PepperCat-YamanekoVillage/NORZ/alu/.alu.png

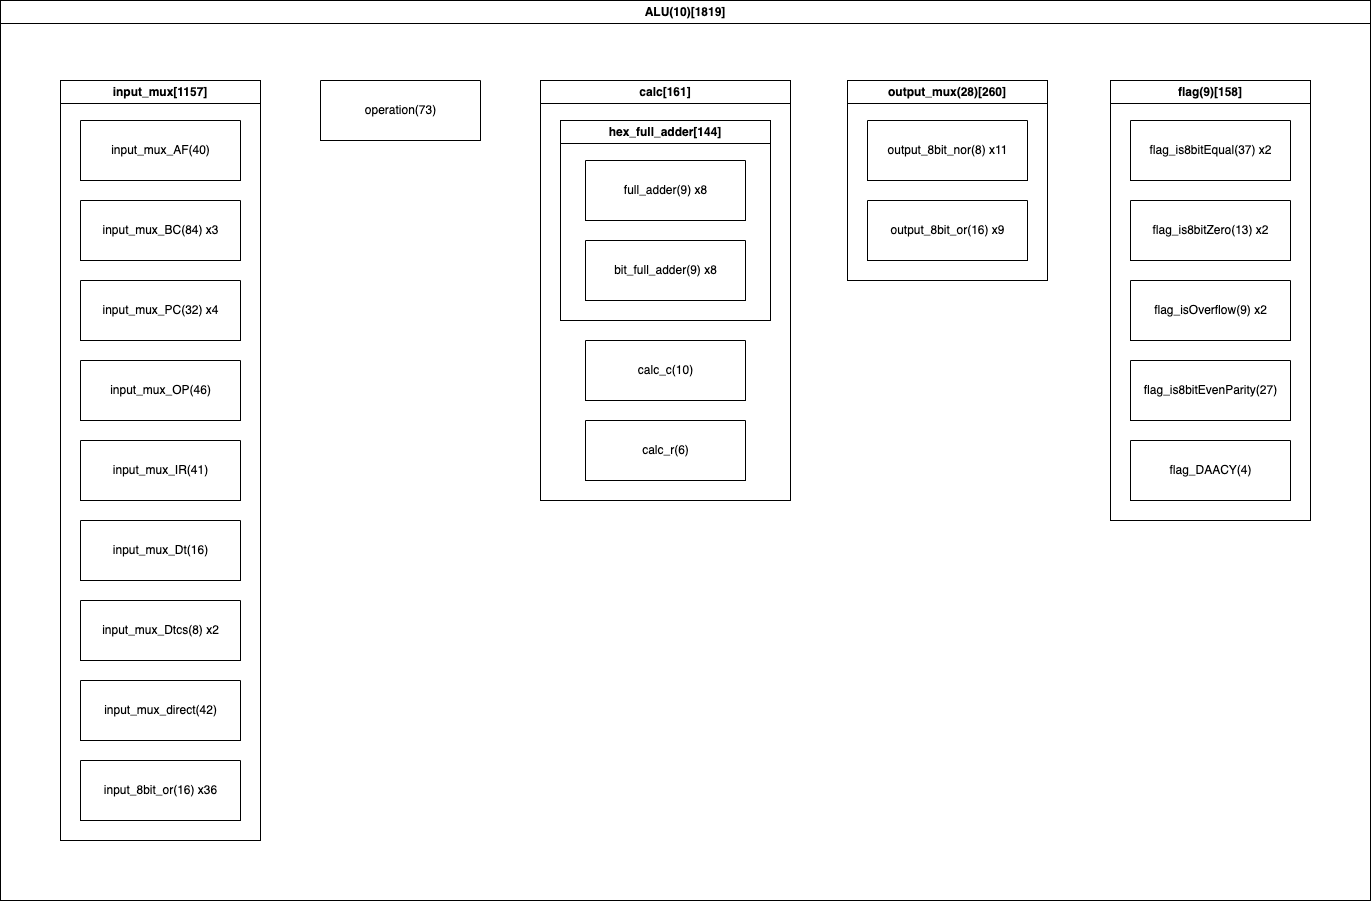
alu/.alu.png
