PepperCat-YamanekoVillage/NORZ/alu/calc/.calc.png

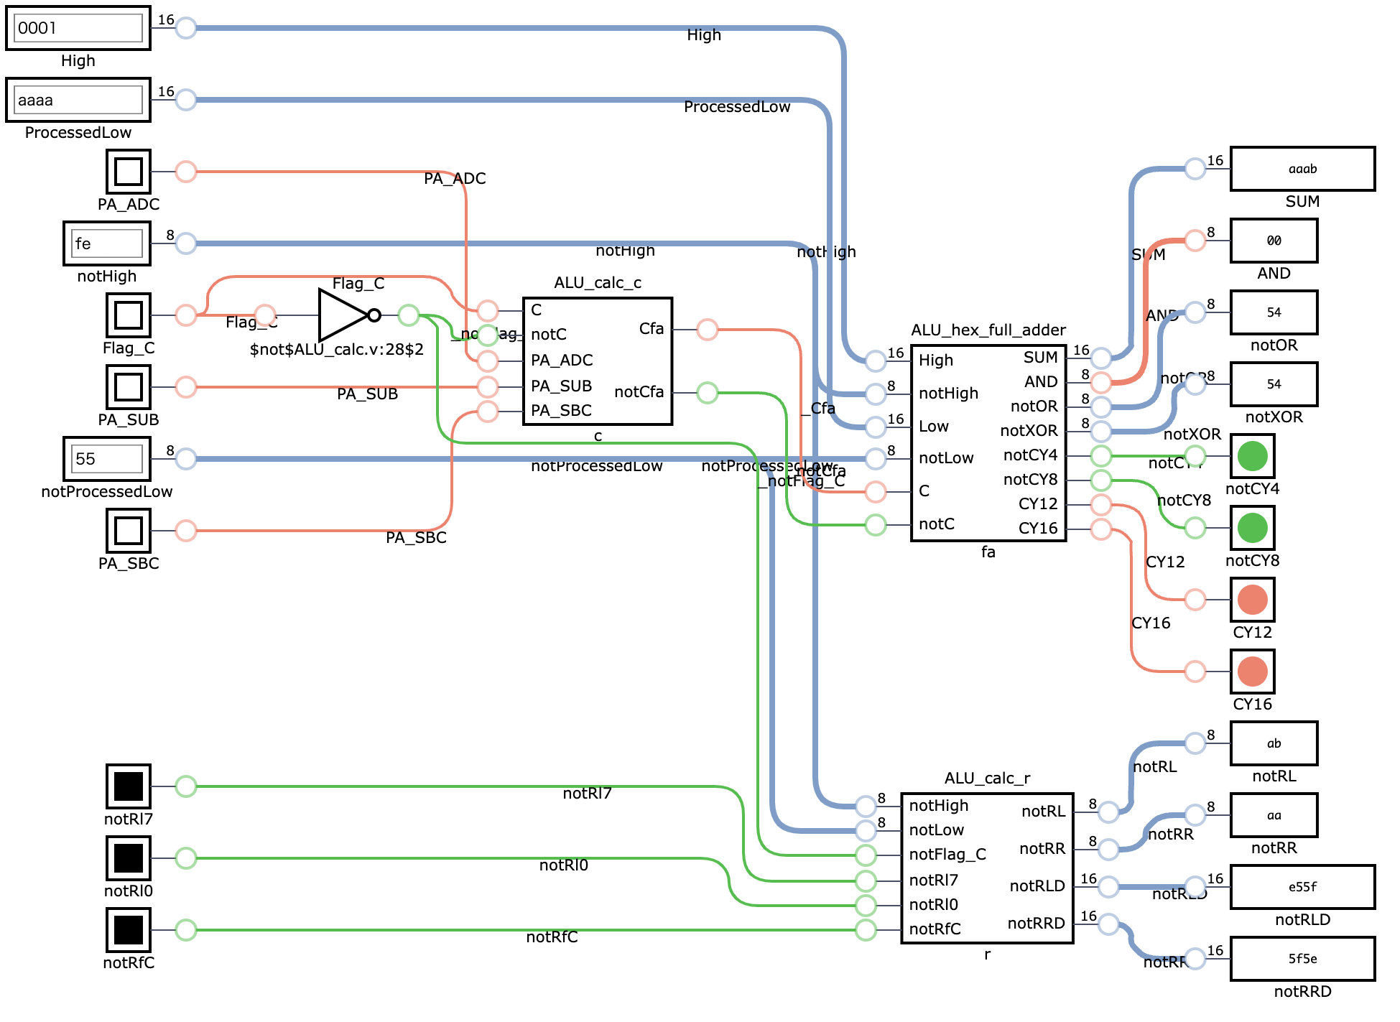
alu/calc/.calc.png
