PepperCat-YamanekoVillage/NORZ/alu/calc/.calc_c.png

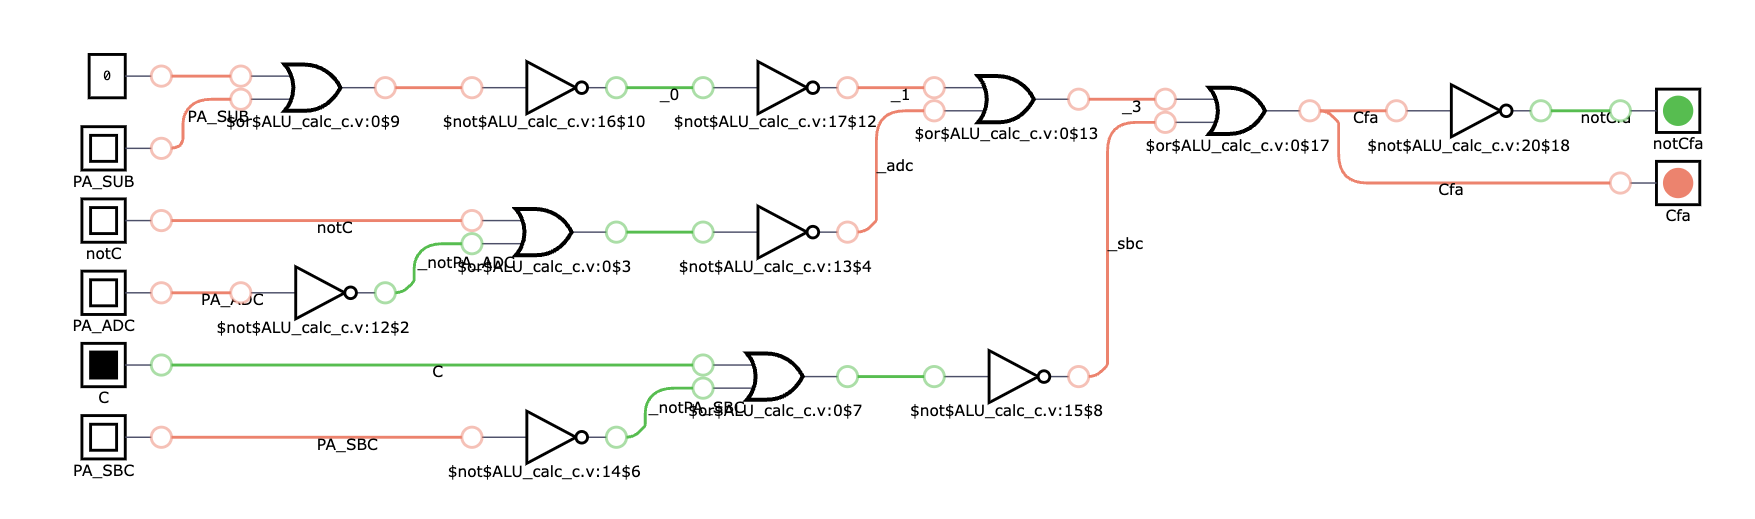
alu/calc/.calc_c.png
