PepperCat-YamanekoVillage/NORZ/alu/calc/.calc_r.png

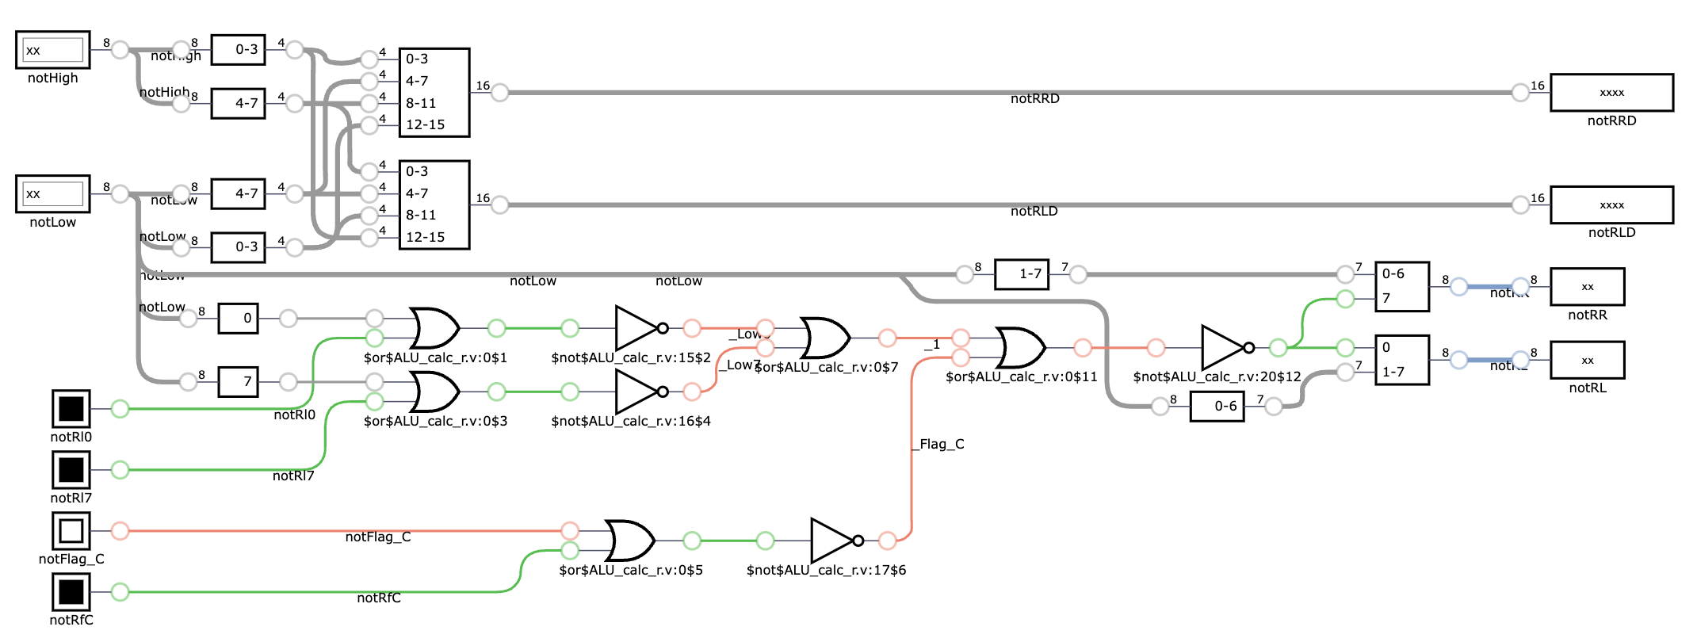
alu/calc/.calc_r.png
