PepperCat-YamanekoVillage/NORZ/alu/calc/full_adder/.bit_full_adder.png

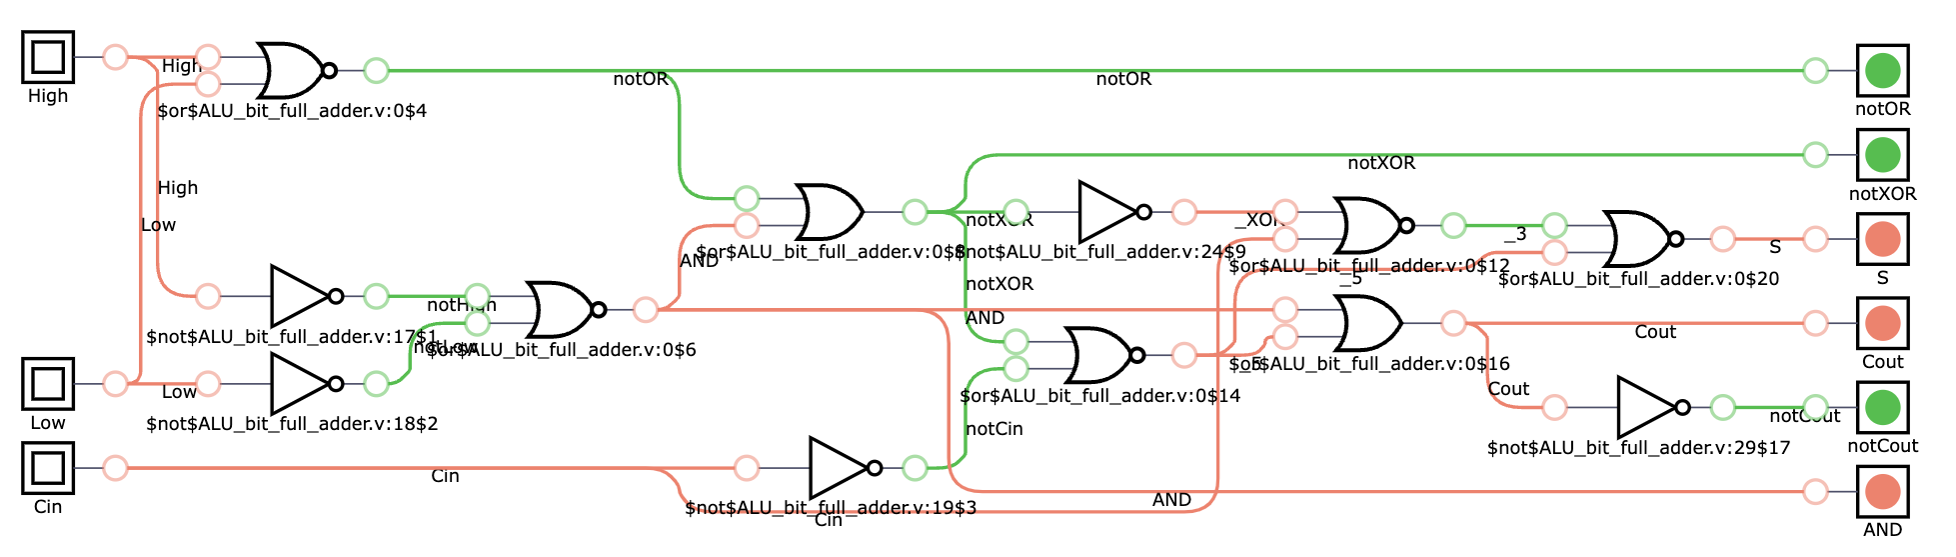
alu/calc/full_adder/.bit_full_adder.png
