PepperCat-YamanekoVillage/NORZ/alu/calc/full_adder/.full_adder.png

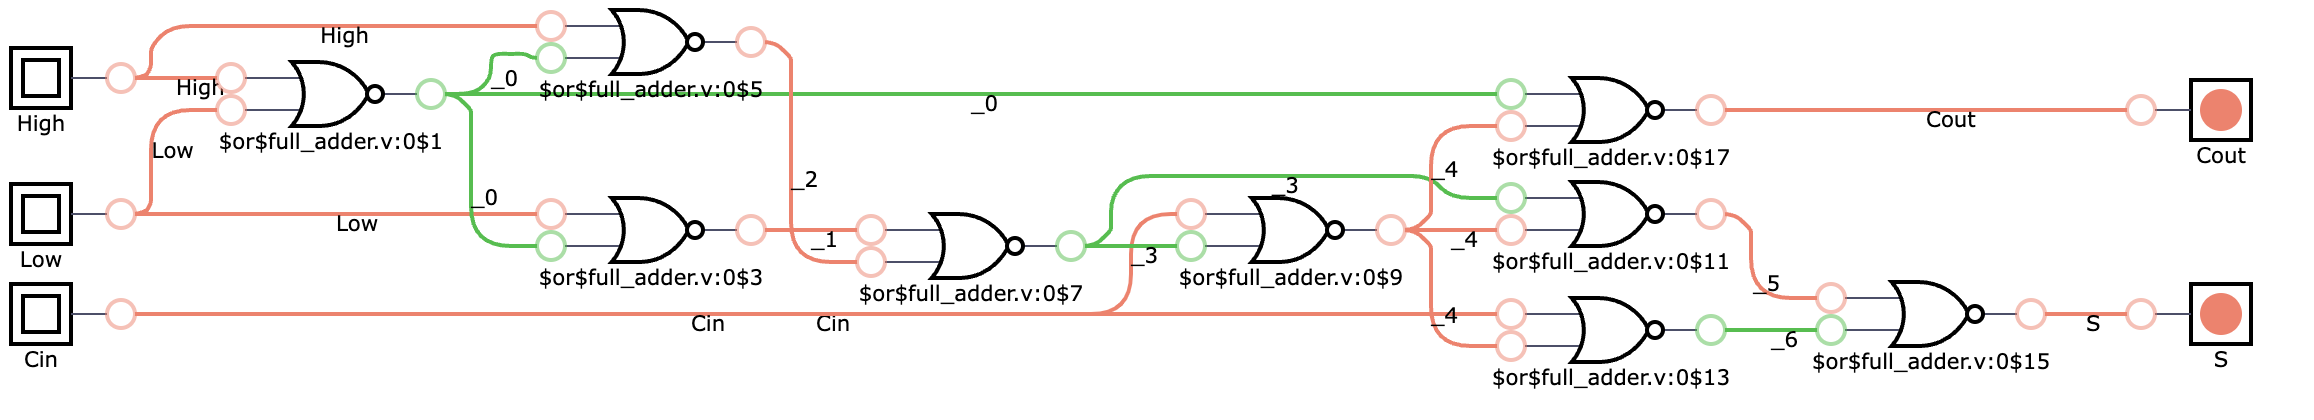
alu/calc/full_adder/.full_adder.png
