PepperCat-YamanekoVillage/NORZ/alu/flag/.flag_is8bitEqual.png

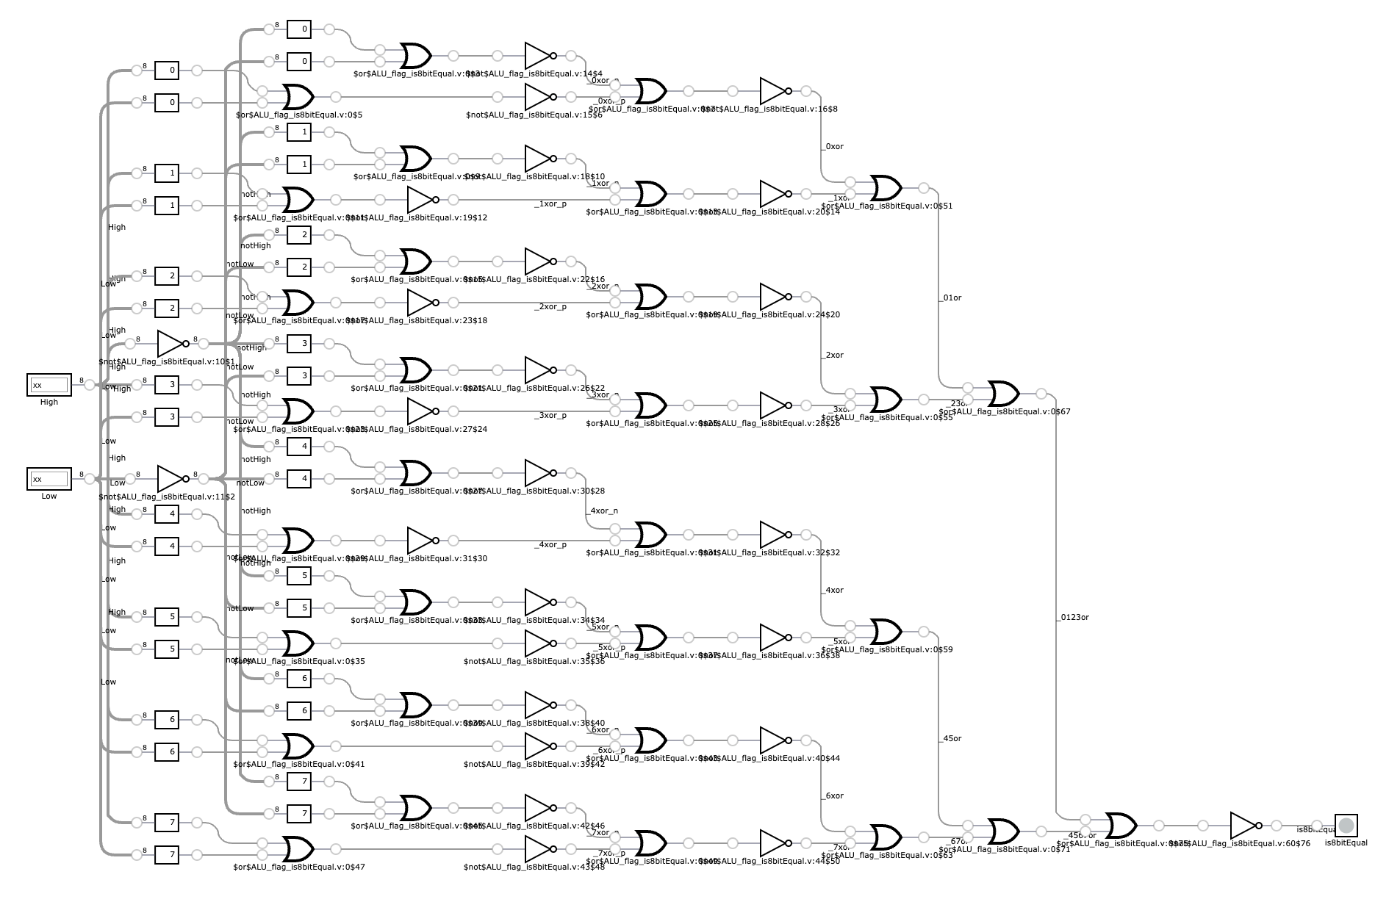
alu/flag/.flag_is8bitEqual.png
