PepperCat-YamanekoVillage/NORZ/alu/flag/.flag_is8bitEvenParity.png

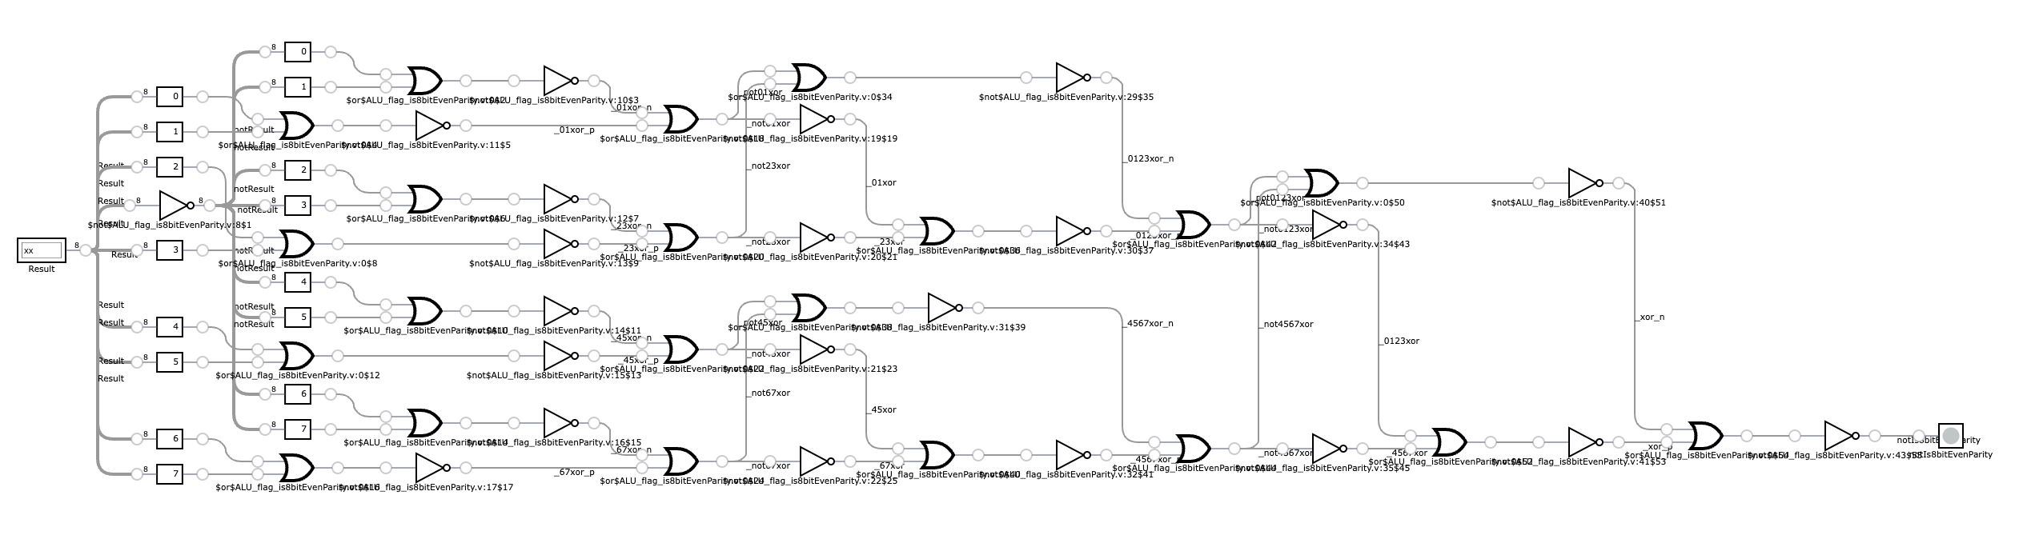
alu/flag/.flag_is8bitEvenParity.png
