PepperCat-YamanekoVillage/NORZ/alu/flag/.flag_is8bitZero.png

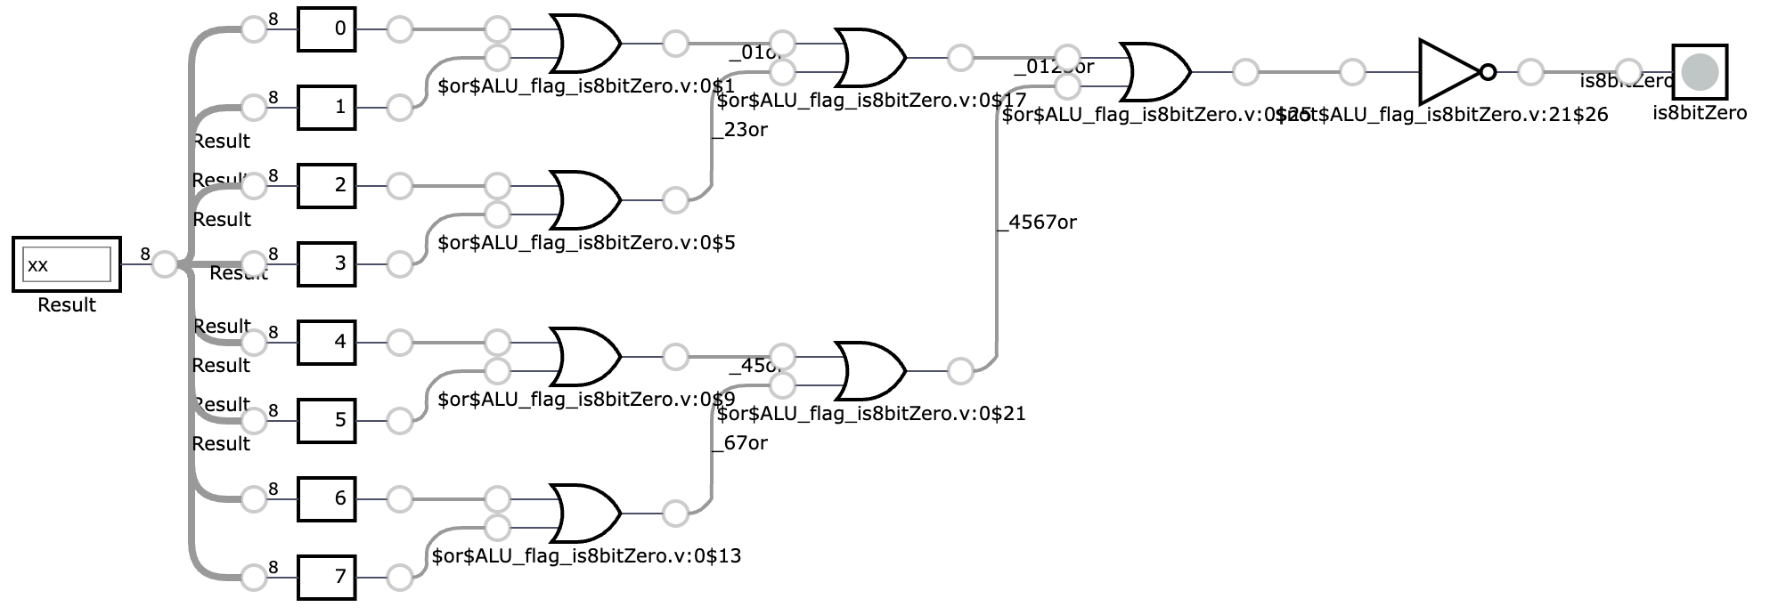
alu/flag/.flag_is8bitZero.png
