PepperCat-YamanekoVillage/NORZ/alu/flag/.flag_isOverflow.png

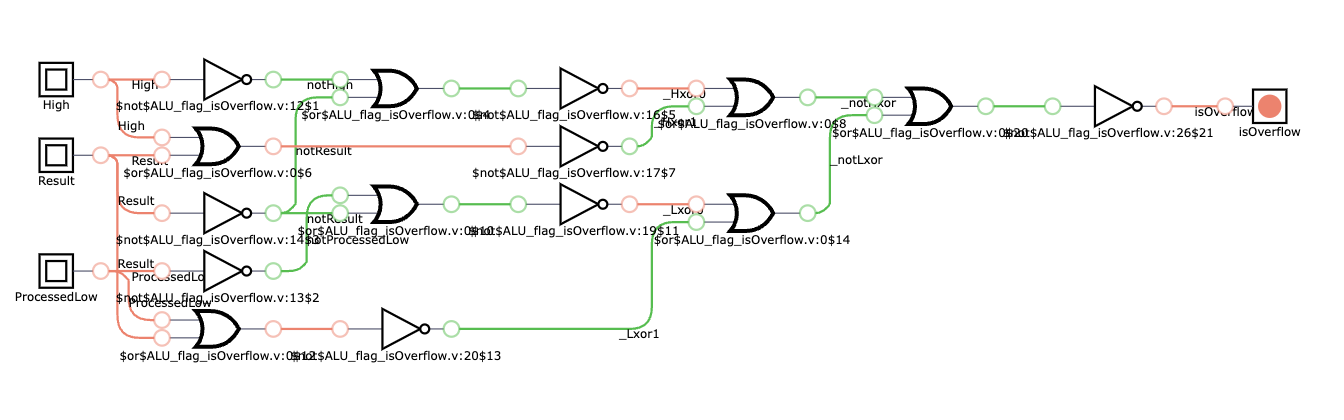
alu/flag/.flag_isOverflow.png
