PepperCat-YamanekoVillage/NORZ/alu/input/.input_8bit_or.png

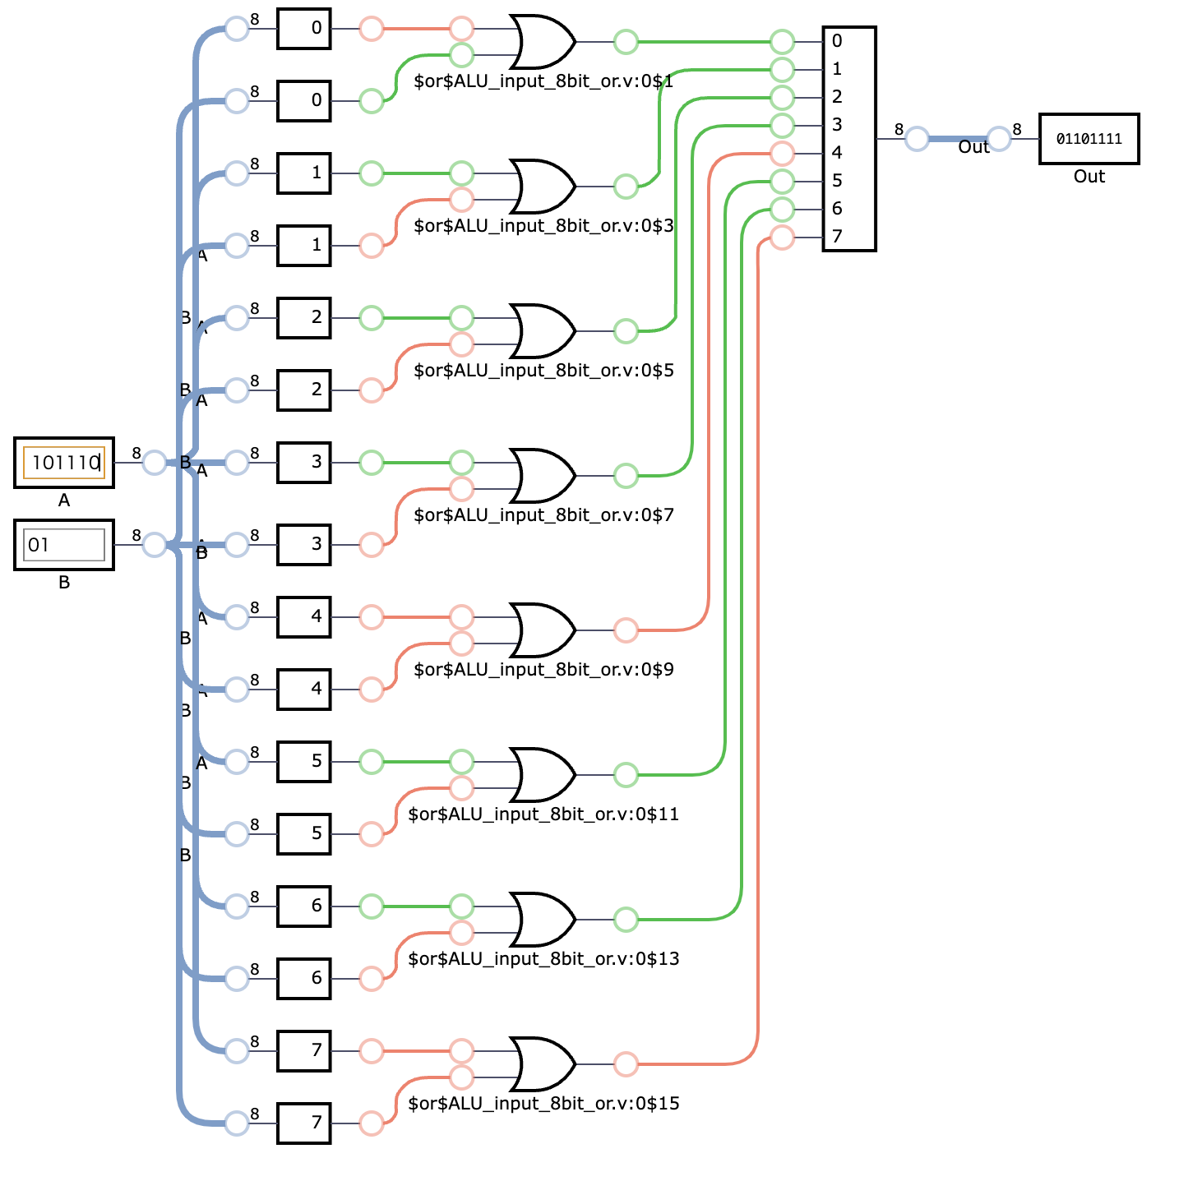
alu/input/.input_8bit_or.png
