PepperCat-YamanekoVillage/NORZ/alu/input/.input_mux_AF.png

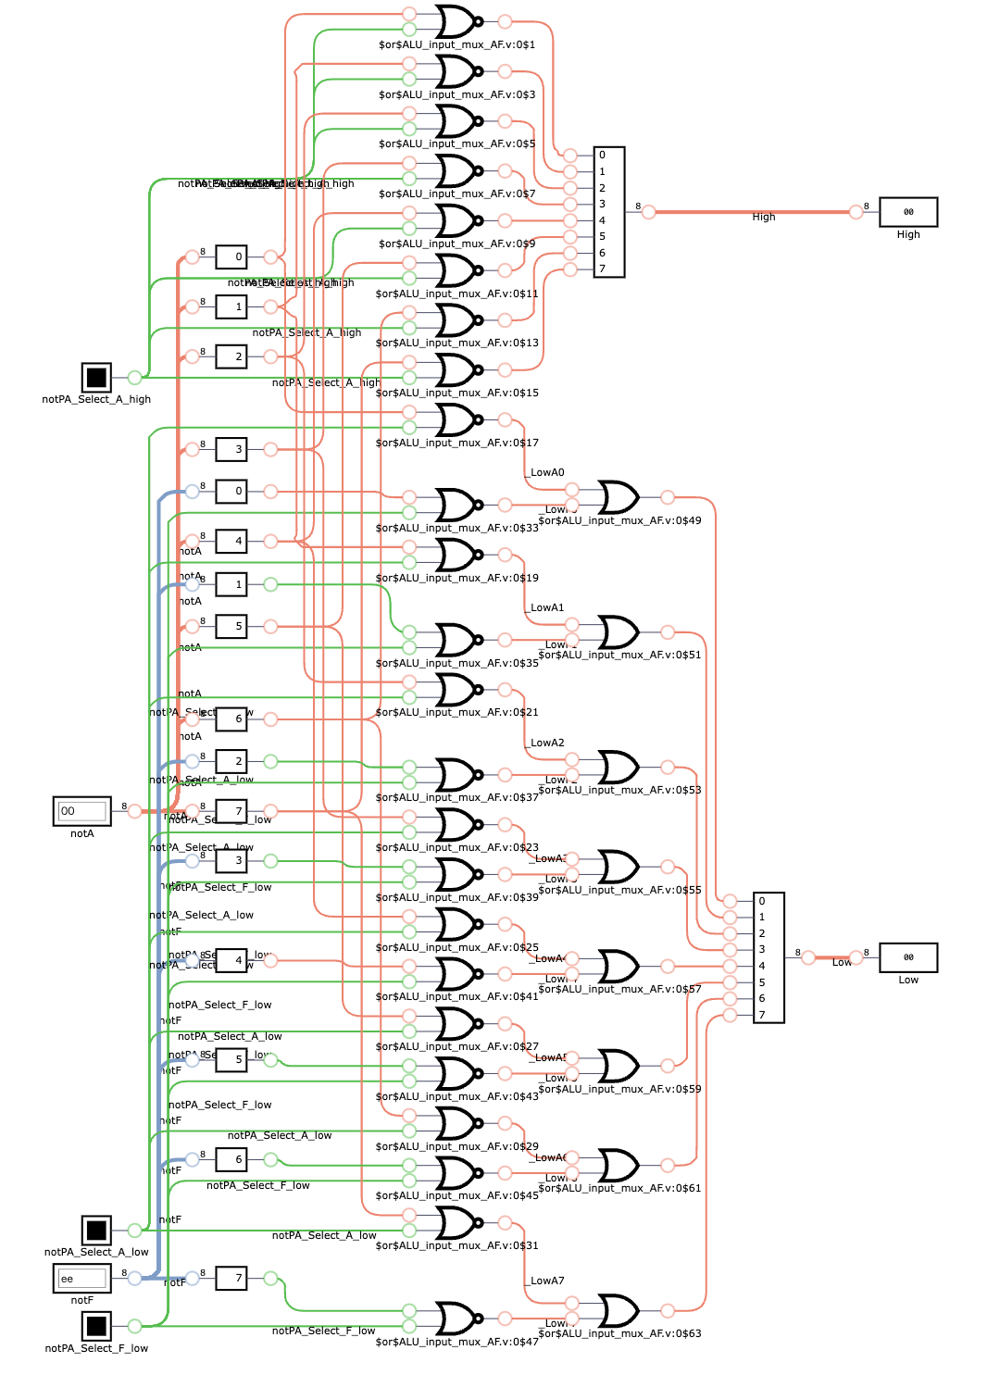
alu/input/.input_mux_AF.png
