PepperCat-YamanekoVillage/NORZ/alu/input/.input_mux_direct.png

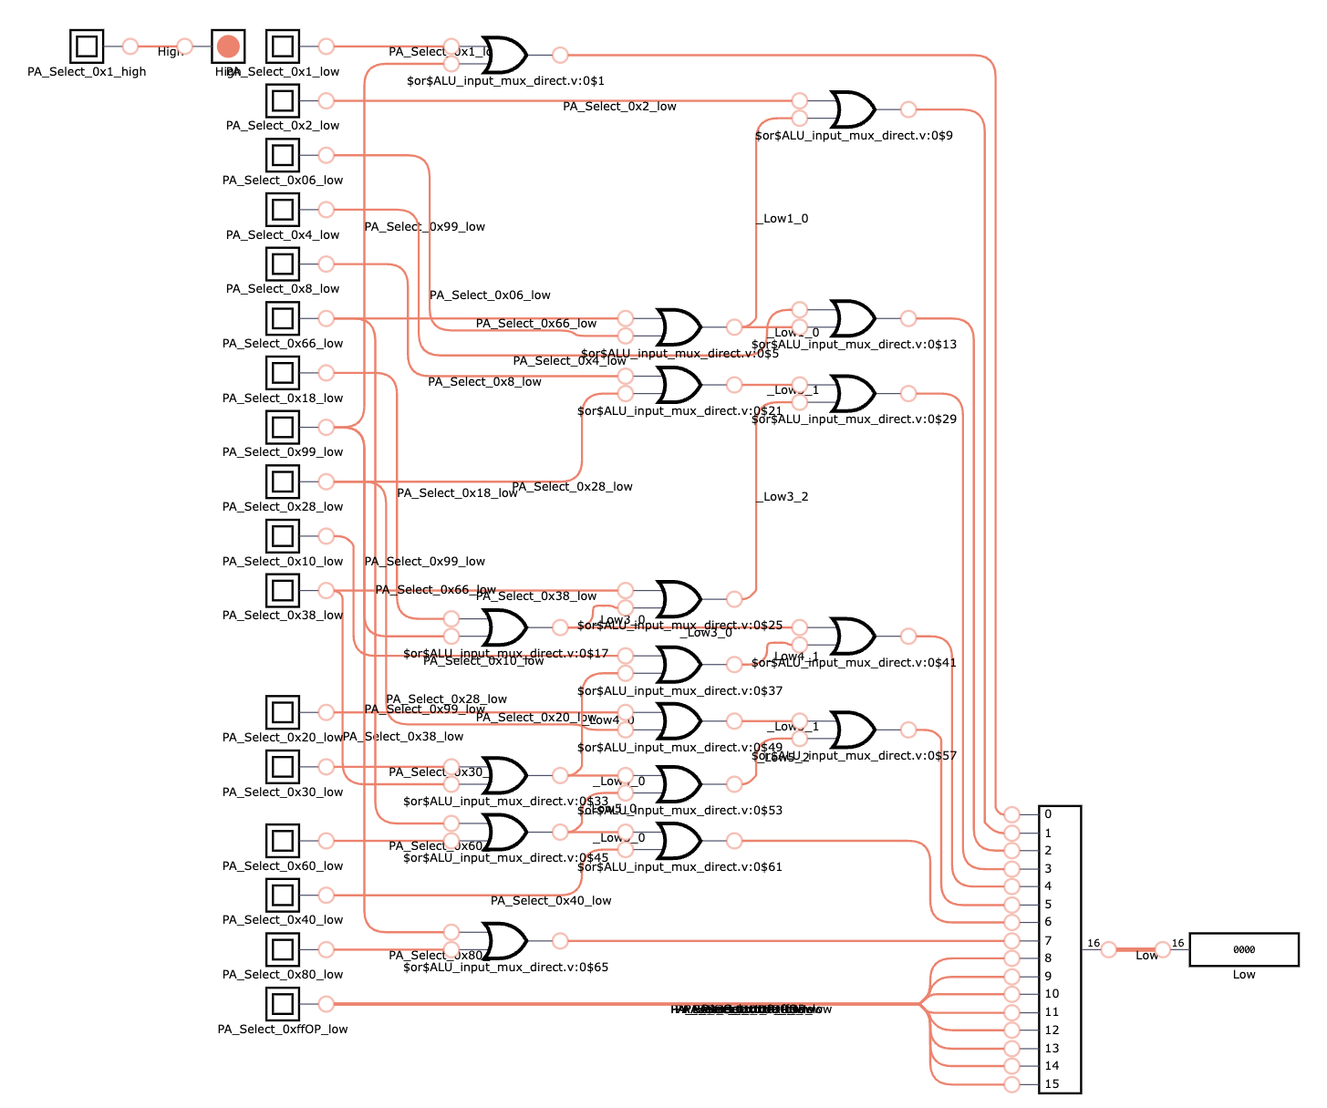
alu/input/.input_mux_direct.png
