PepperCat-YamanekoVillage/NORZ/alu/output/.output_mux.png

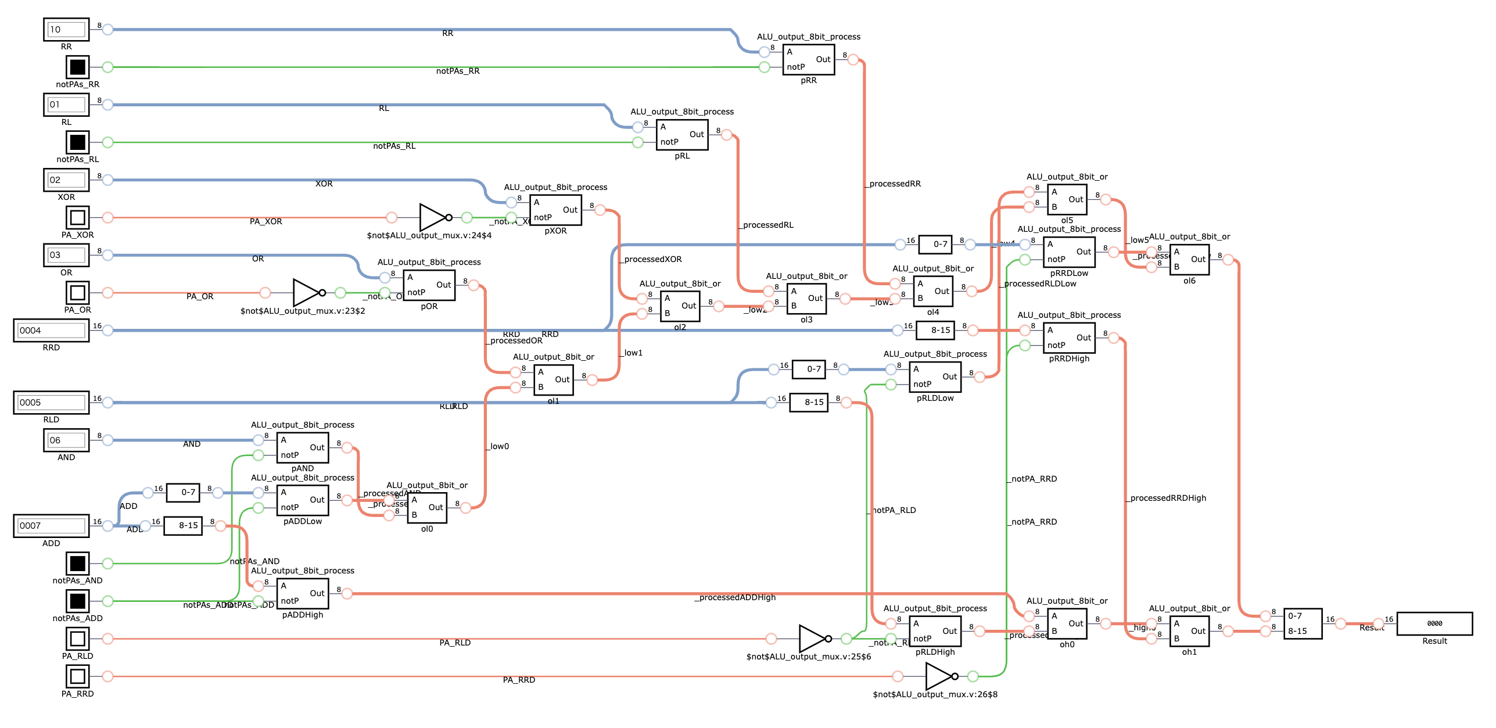
alu/output/.output_mux.png
