PepperCat-YamanekoVillage/NORZ/decoder/.decoder.png

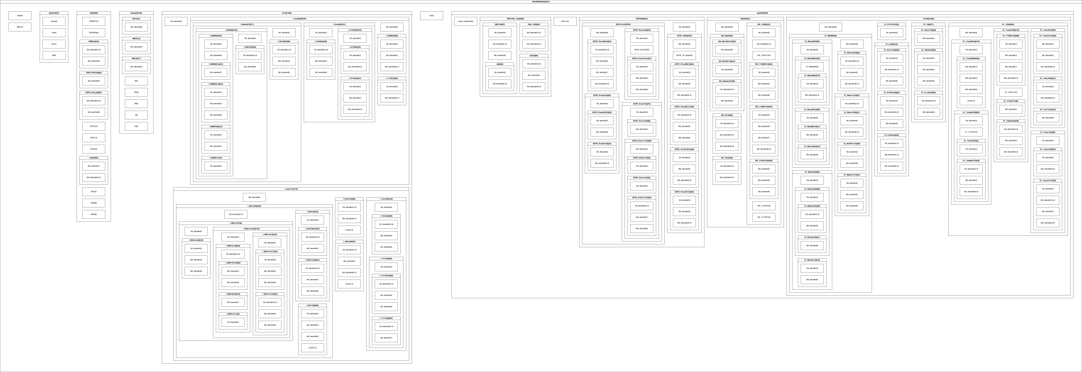
decoder/.decoder.png
