PepperCat-YamanekoVillage/NORZ/decoder/.reset.png

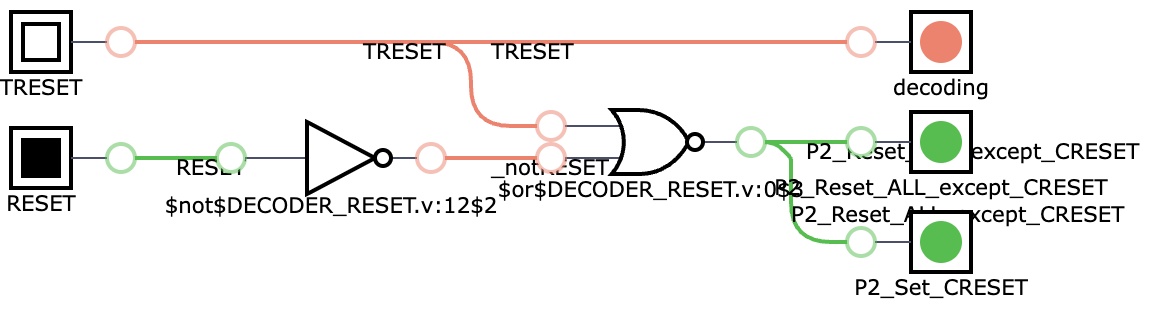
decoder/.reset.png
