PepperCat-YamanekoVillage/NORZ/decoder/basic/.I.png

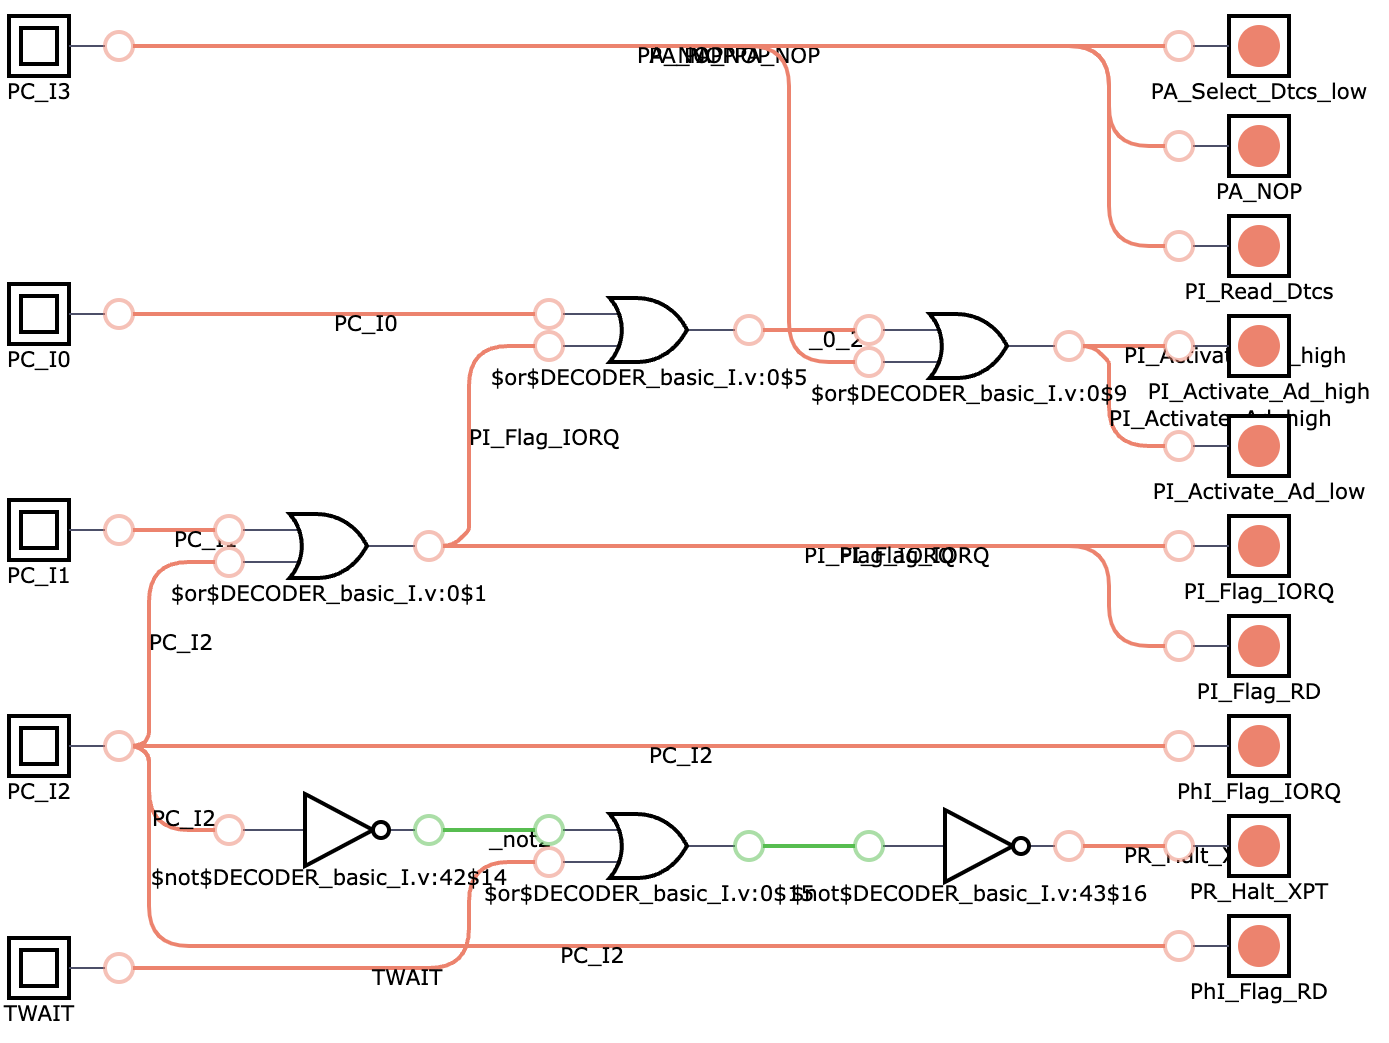
decoder/basic/.I.png
