PepperCat-YamanekoVillage/NORZ/decoder/basic/.M1.png

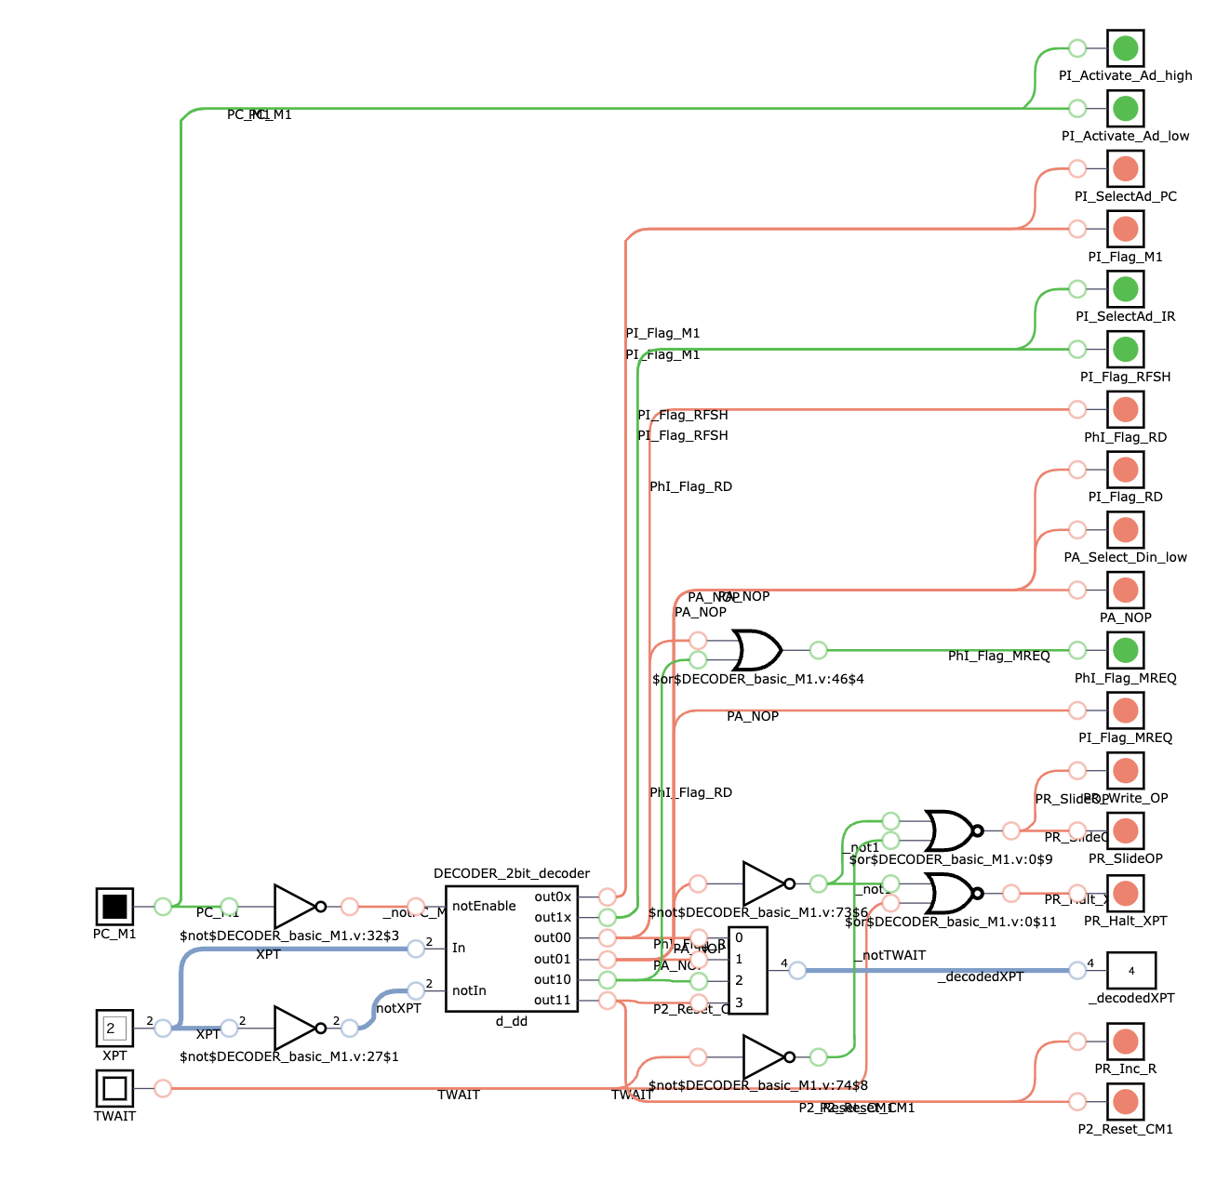
decoder/basic/.M1.png
