PepperCat-YamanekoVillage/NORZ/decoder/basic/.MA.png

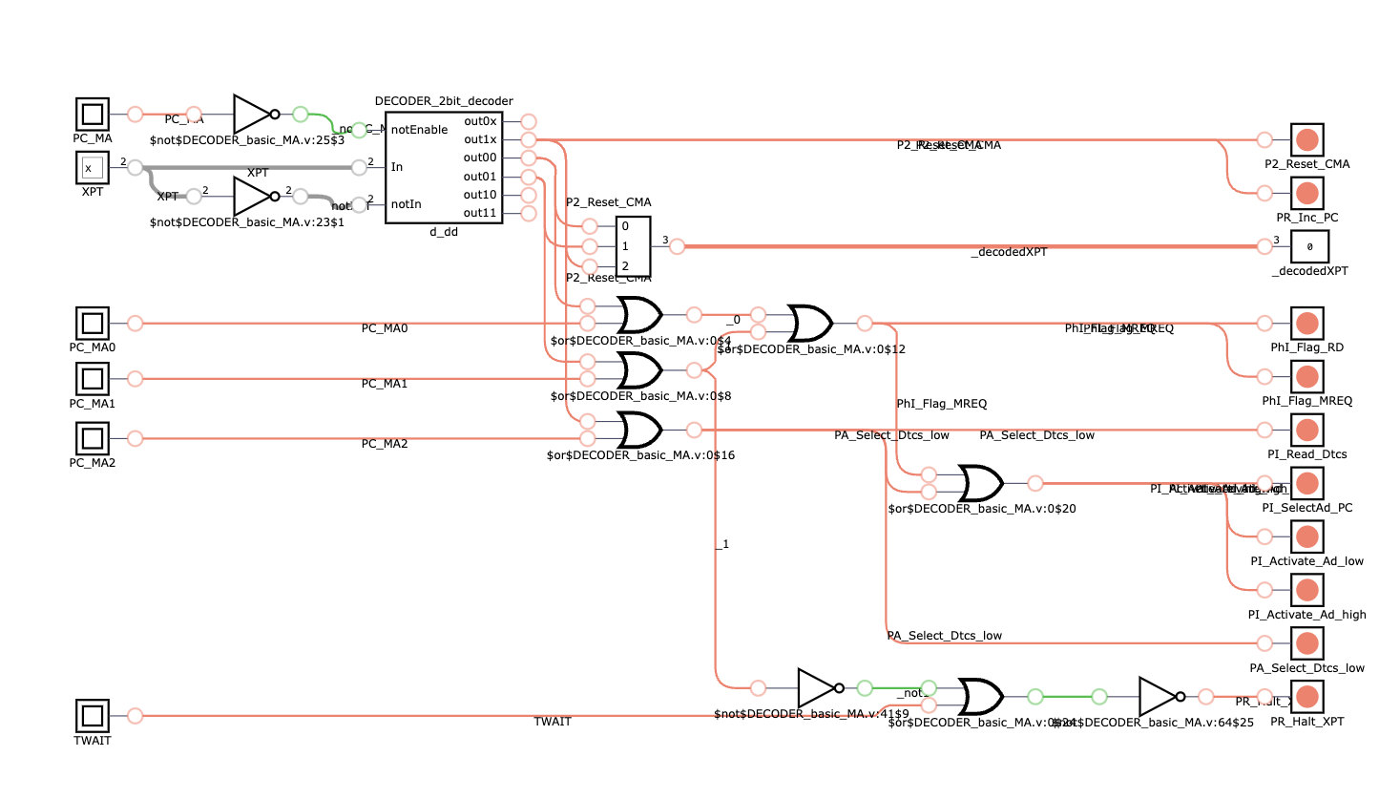
decoder/basic/.MA.png
