PepperCat-YamanekoVillage/NORZ/decoder/basic/.MR.png

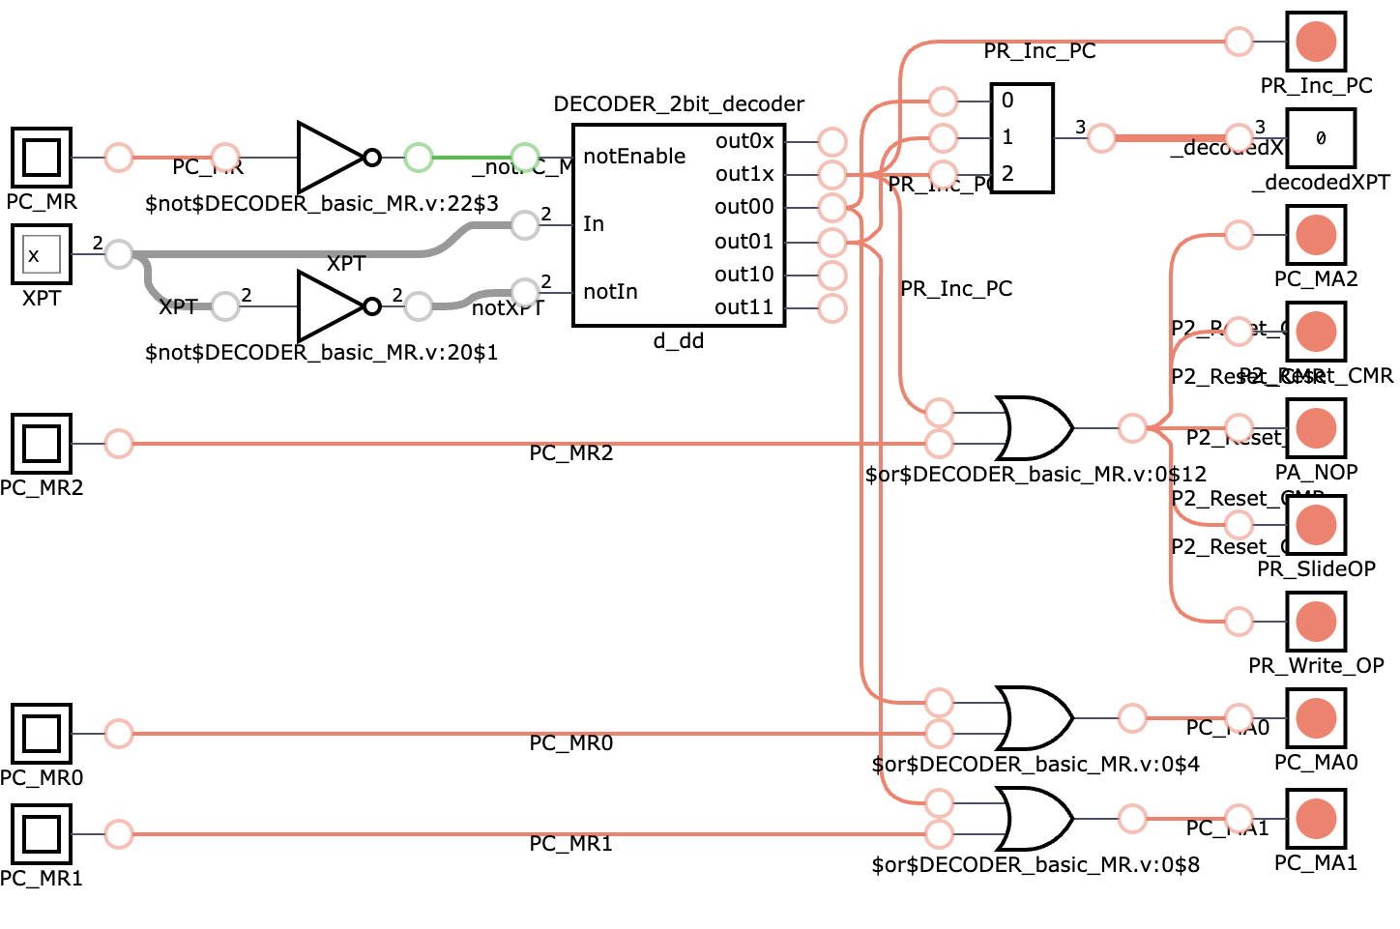
decoder/basic/.MR.png
