PepperCat-YamanekoVillage/NORZ/decoder/basic/.O.png

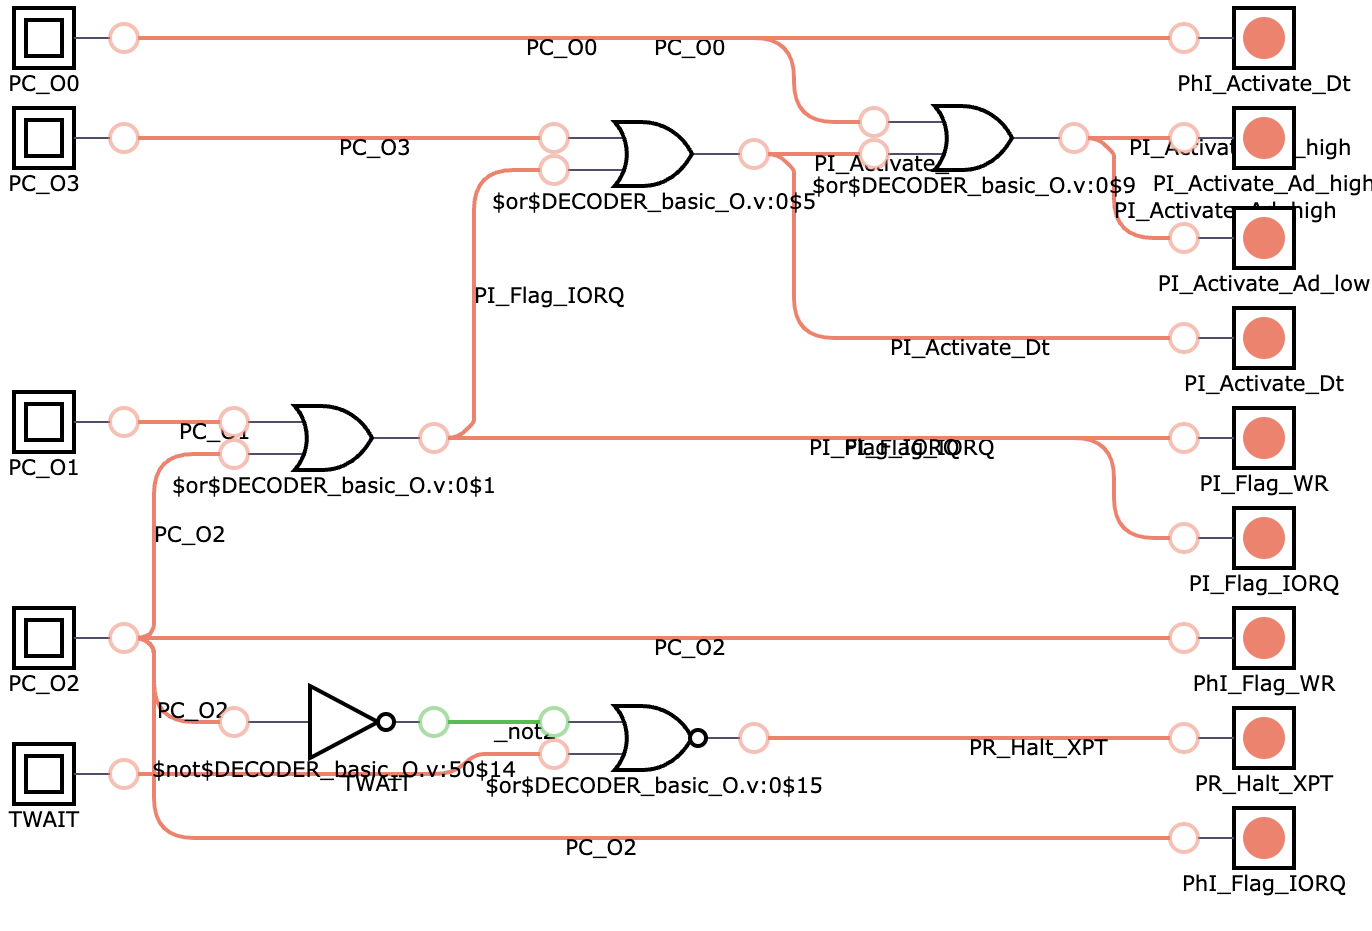
decoder/basic/.O.png
