PepperCat-YamanekoVillage/NORZ/decoder/basic/.RA.png

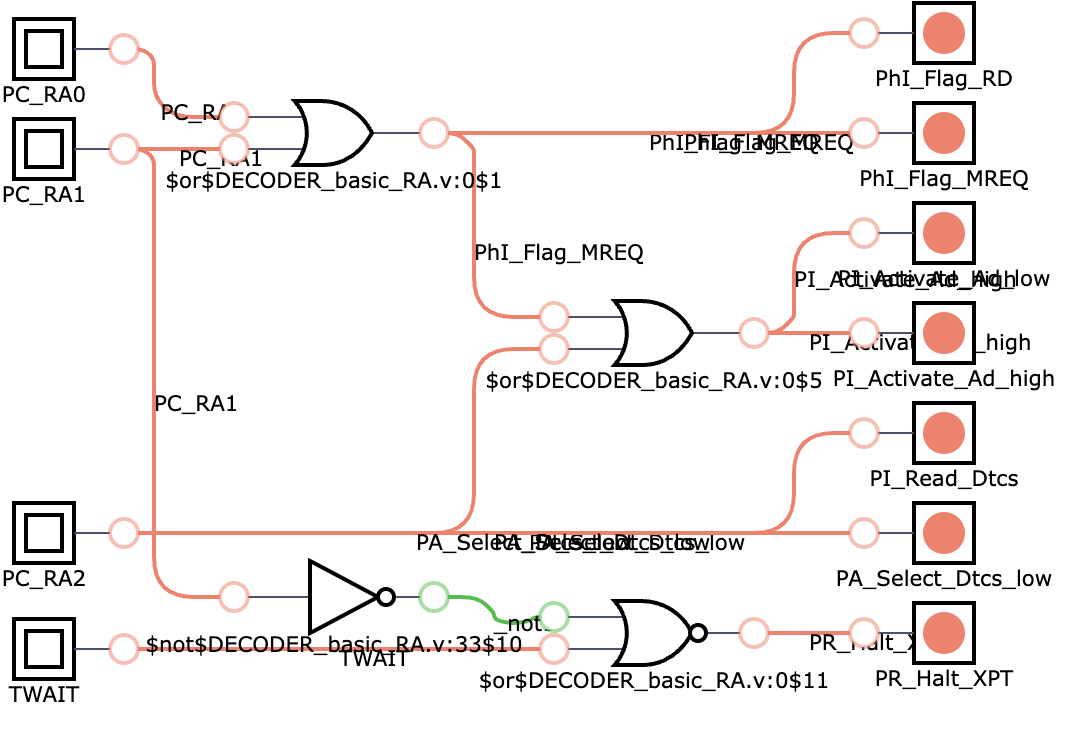
decoder/basic/.RA.png
