PepperCat-YamanekoVillage/NORZ/decoder/basic/.W.png

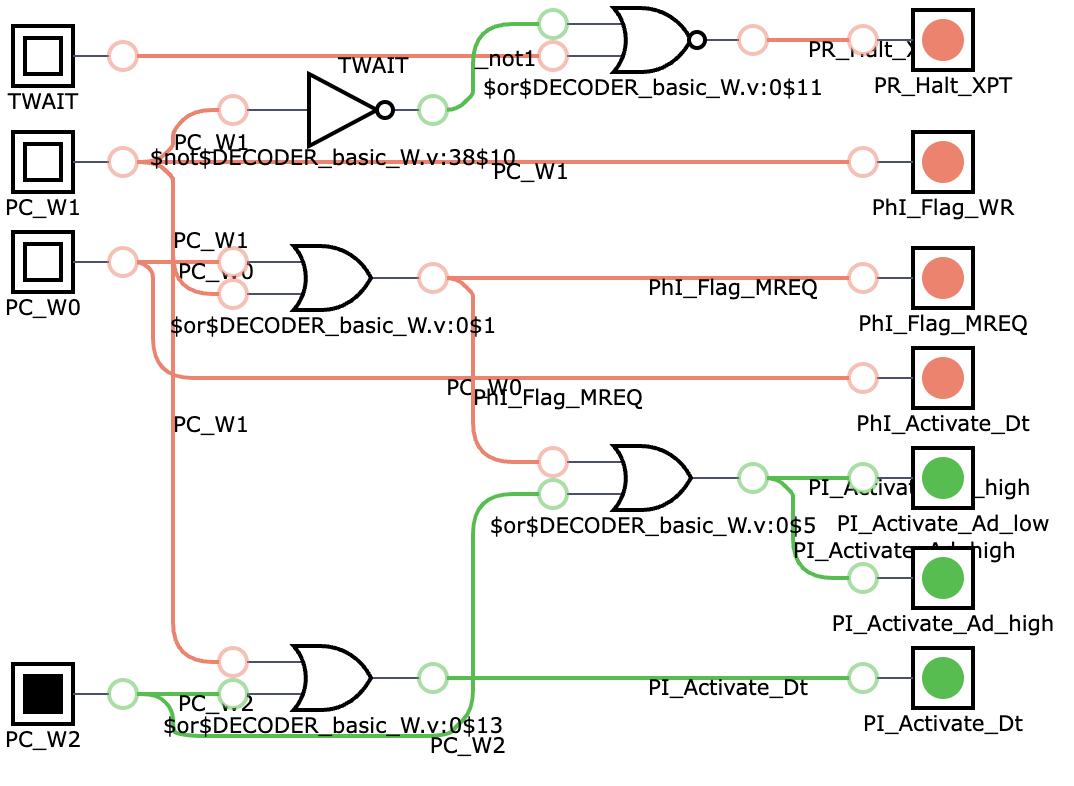
decoder/basic/.W.png
