PepperCat-YamanekoVillage/NORZ/decoder/C/.CBUSRQ.png

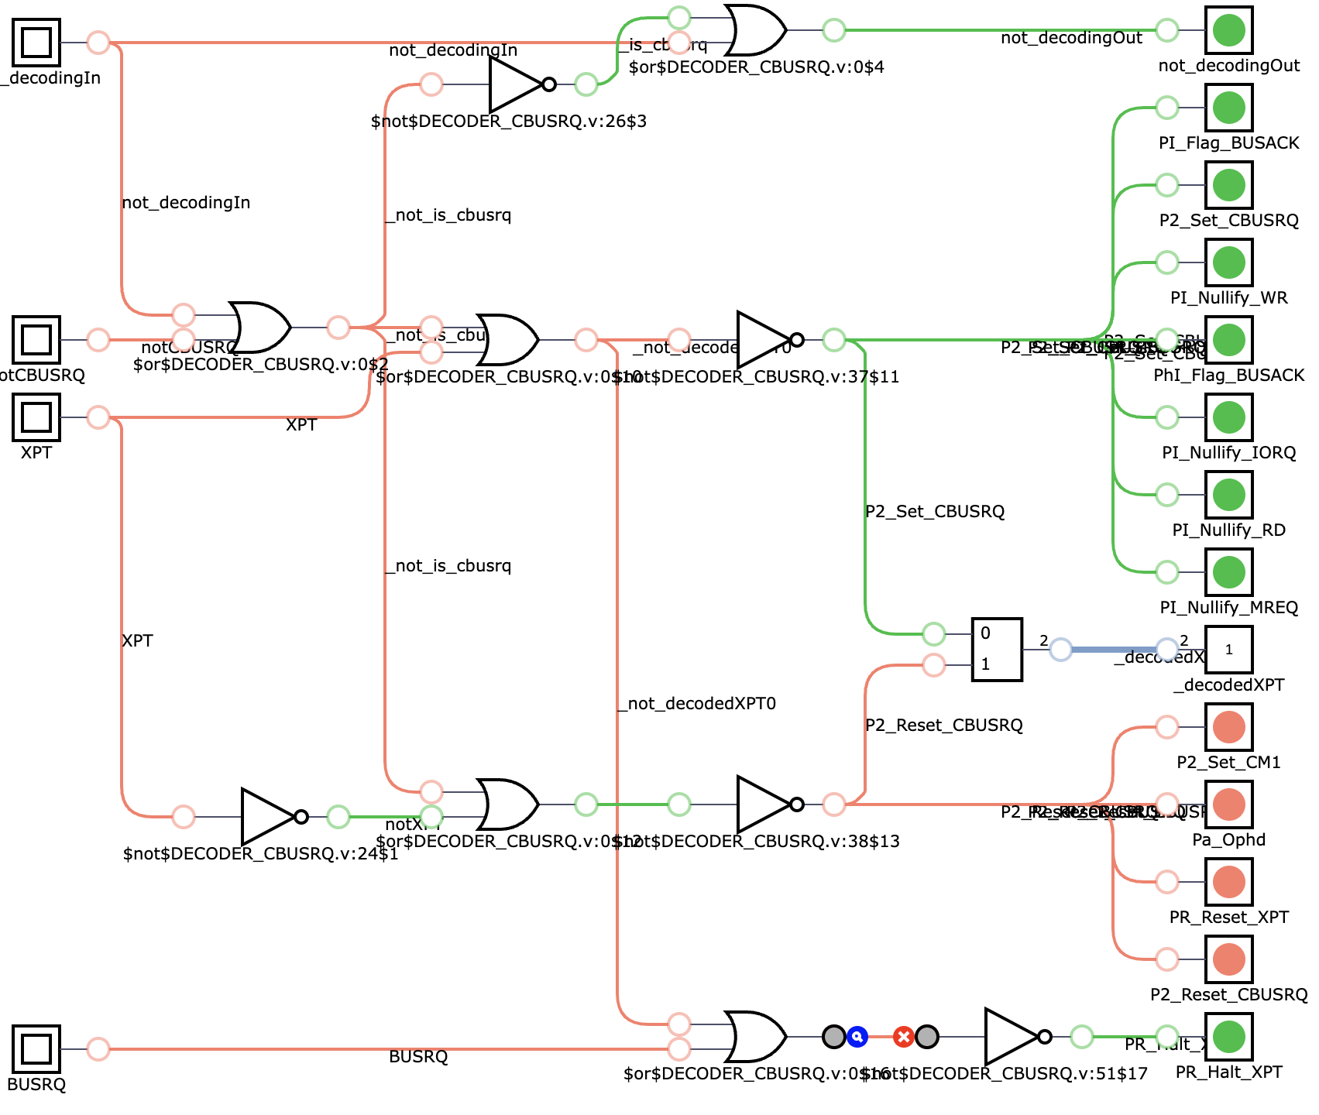
decoder/C/.CBUSRQ.png
