PepperCat-YamanekoVillage/NORZ/decoder/C/.CINT0.png

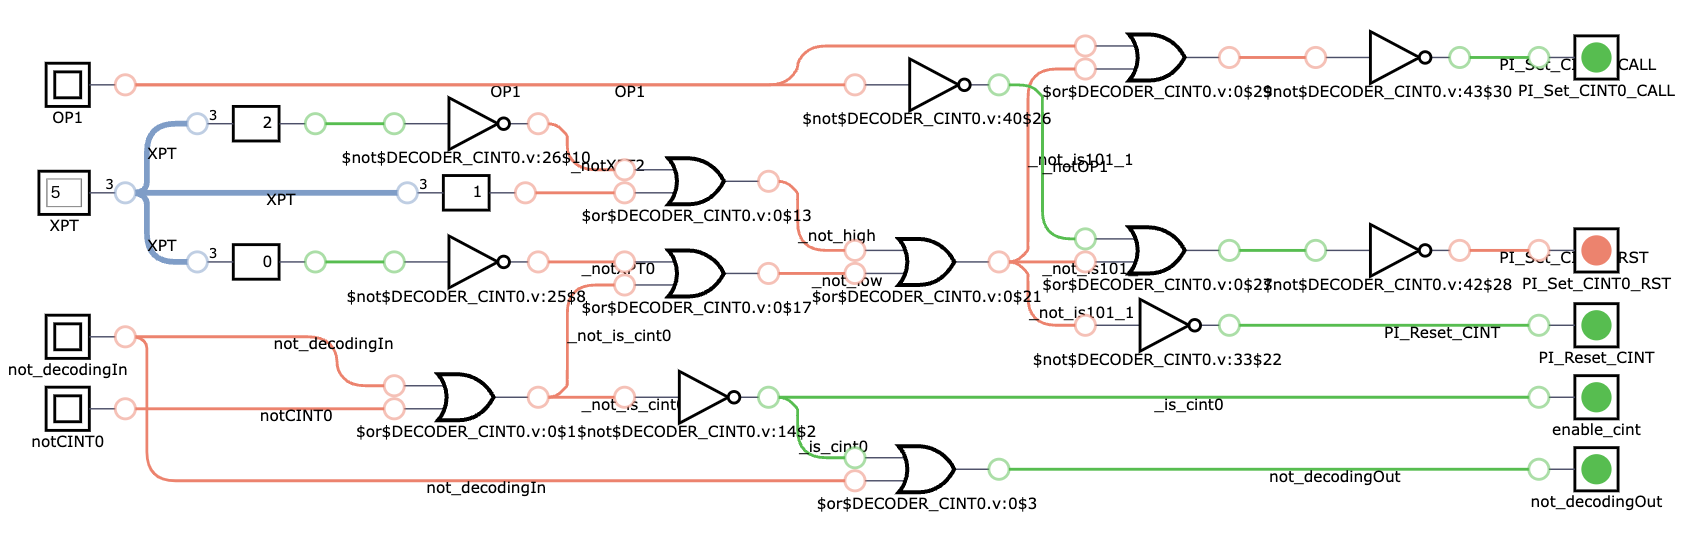
decoder/C/.CINT0.png
