PepperCat-YamanekoVillage/NORZ/decoder/C/.CINT1.png

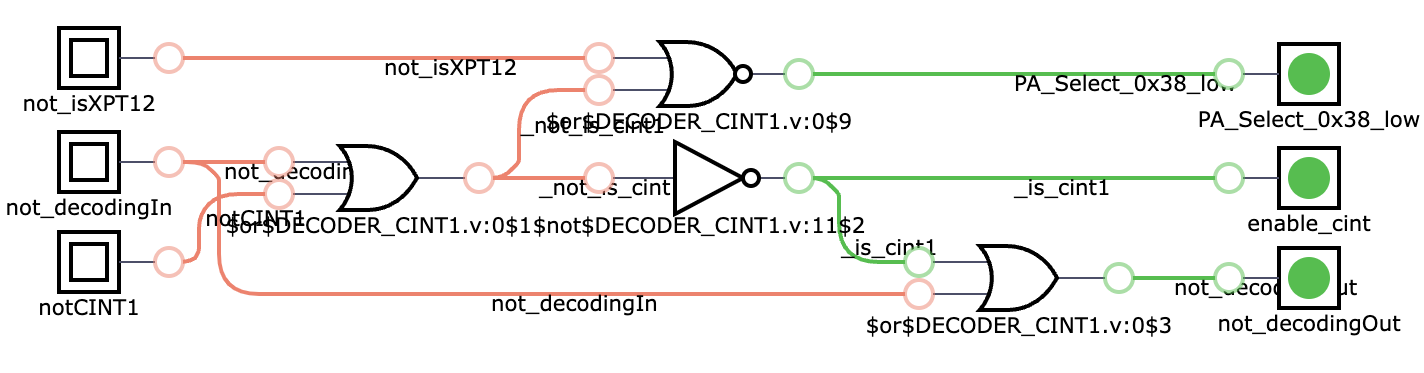
decoder/C/.CINT1.png
