PepperCat-YamanekoVillage/NORZ/decoder/C/.CM1.png

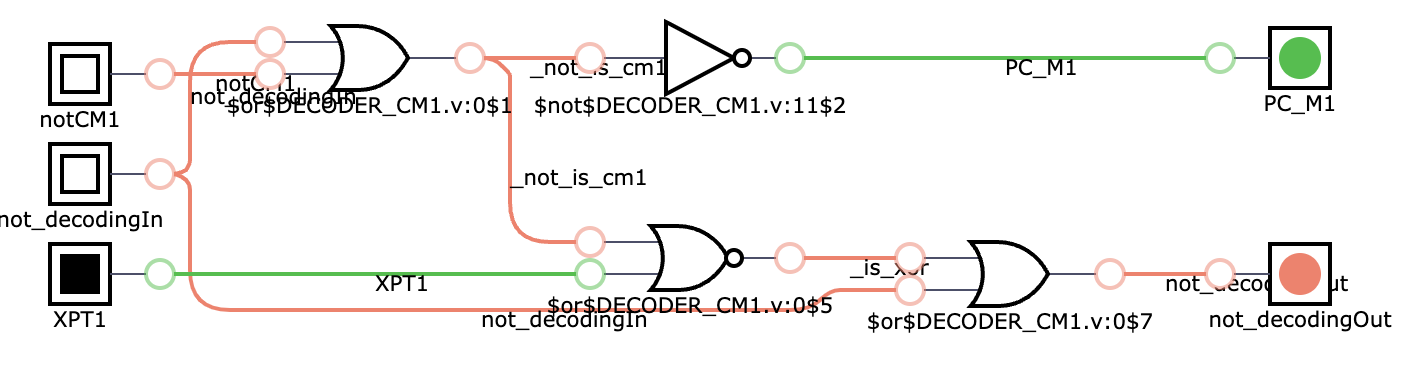
decoder/C/.CM1.png
