PepperCat-YamanekoVillage/NORZ/decoder/C/.CMR.png

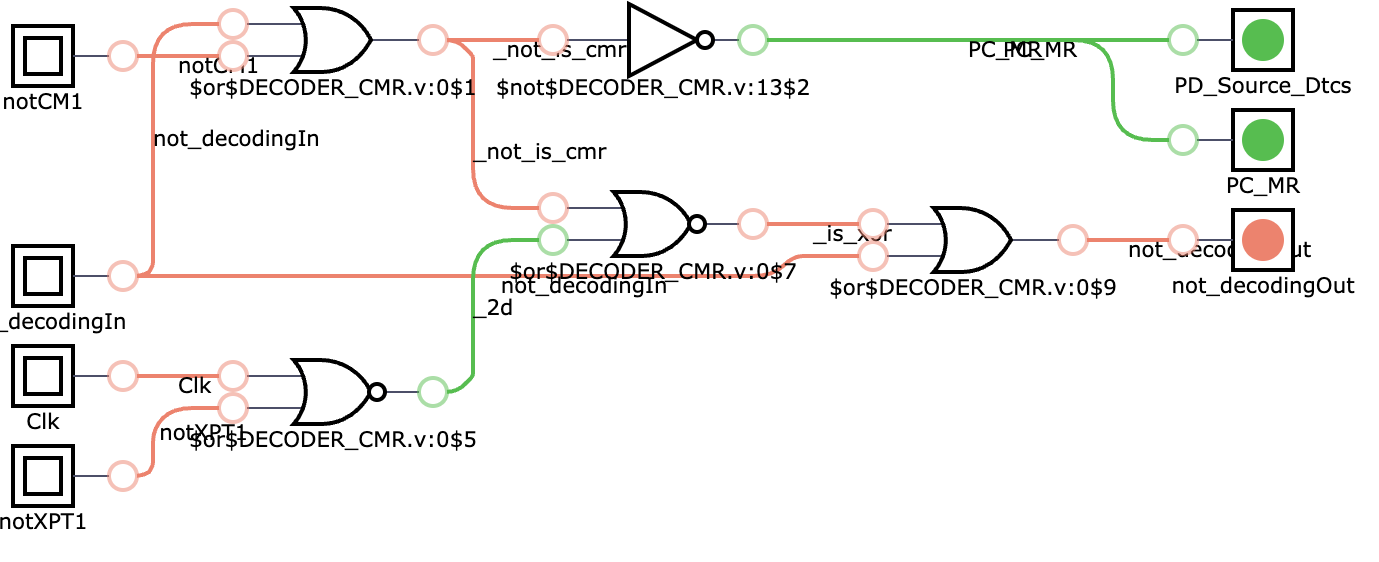
decoder/C/.CMR.png
