PepperCat-YamanekoVillage/NORZ/decoder/C/.CRESET.png

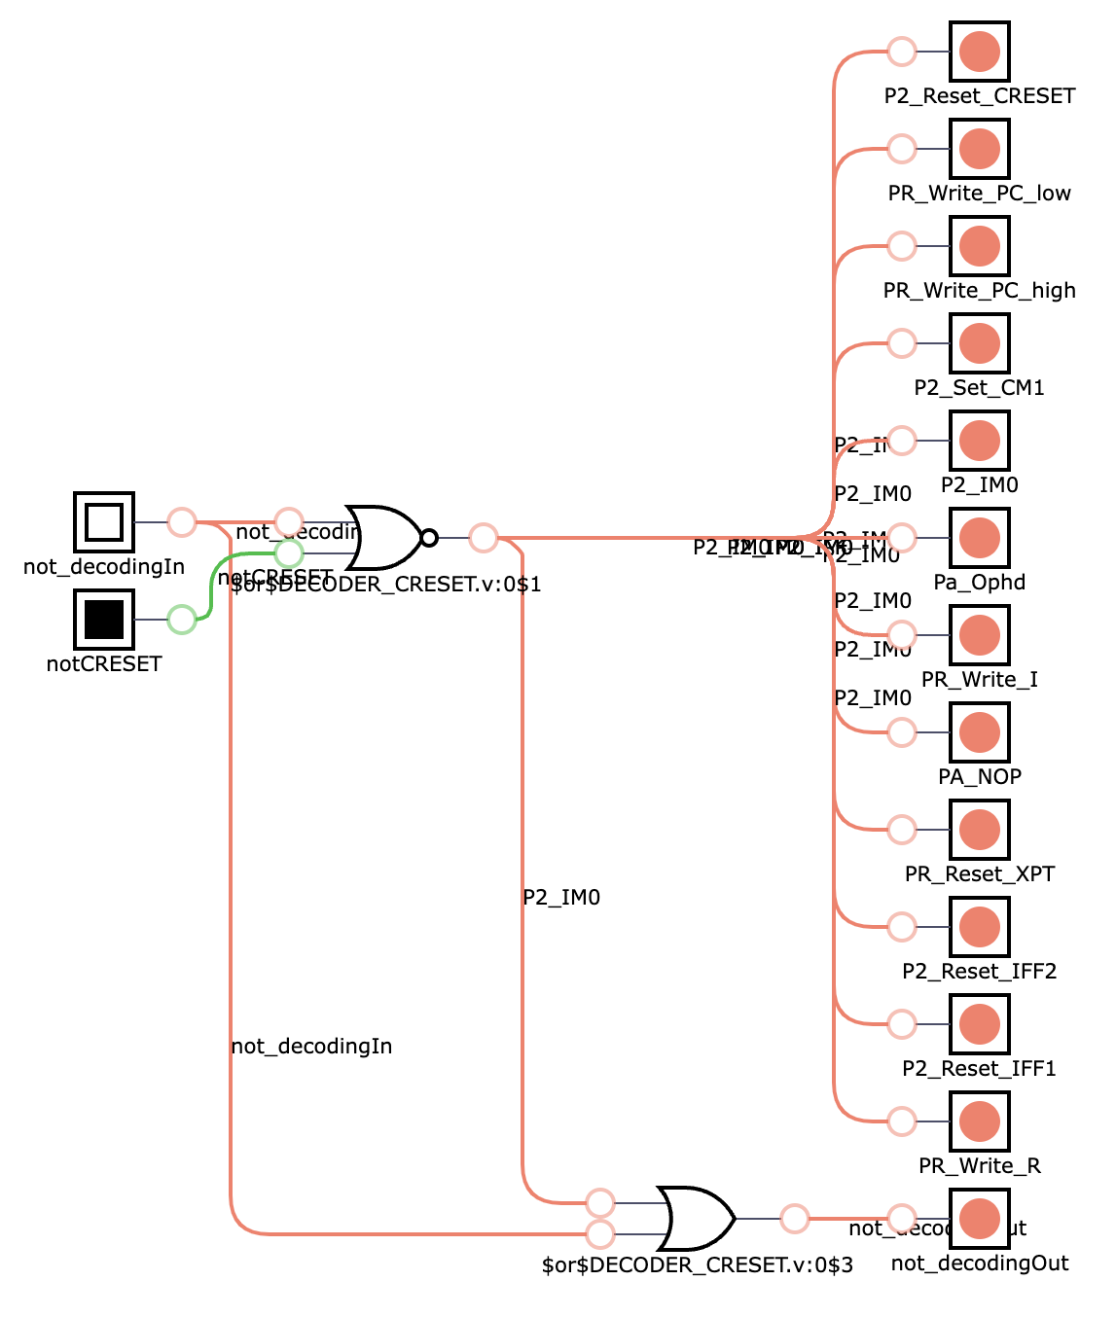
decoder/C/.CRESET.png
