PepperCat-YamanekoVillage/NORZ/decoder/op/.source_selecter.png

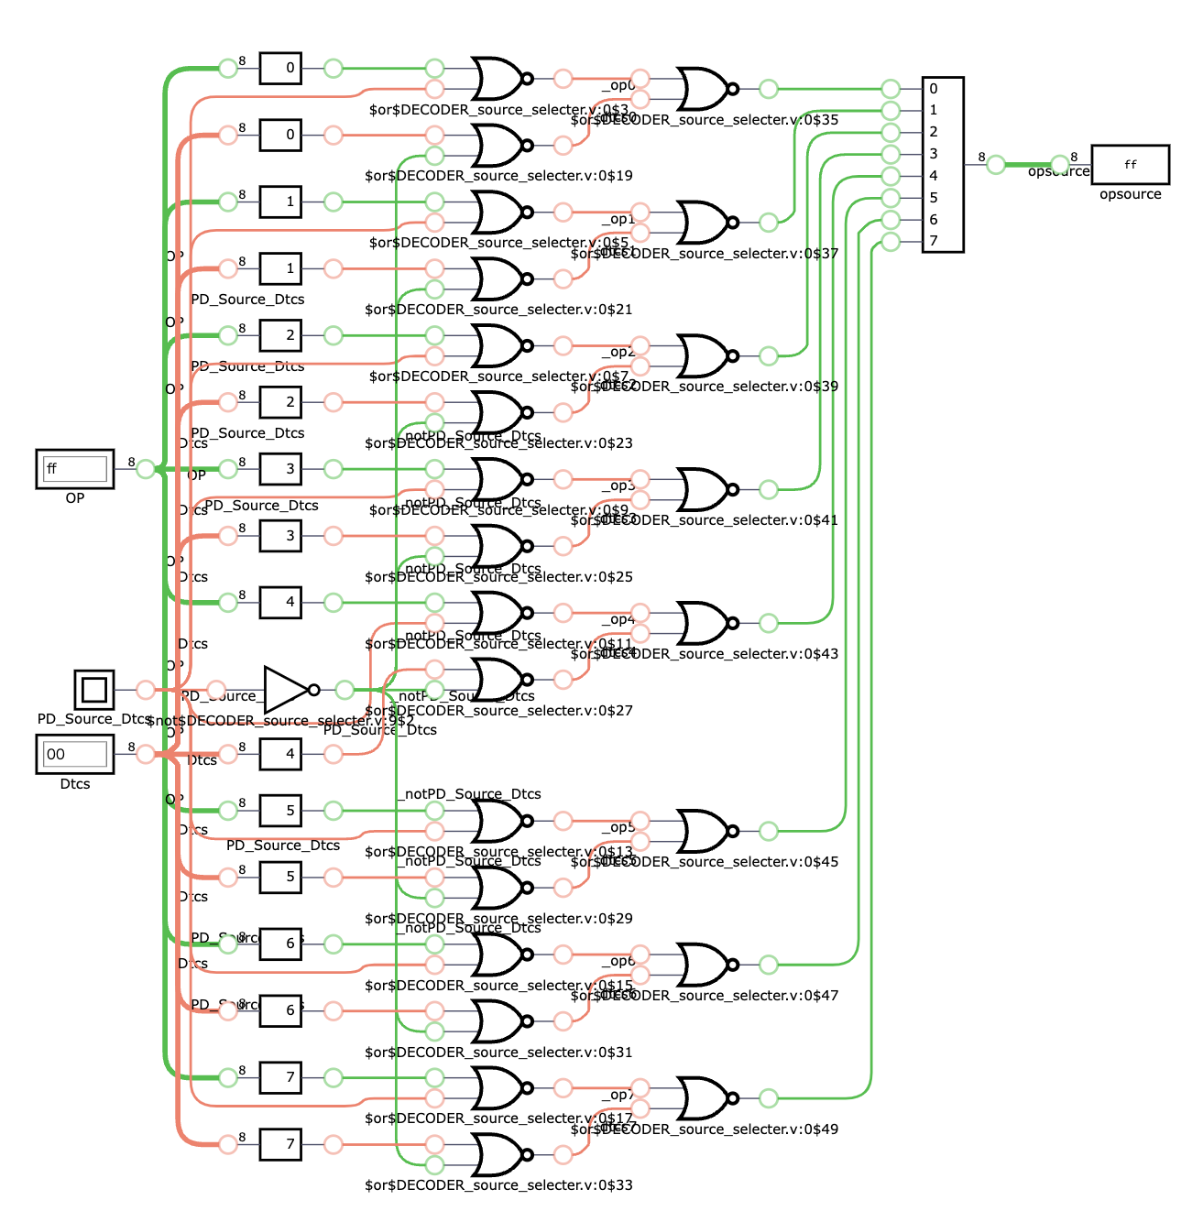
decoder/op/.source_selecter.png
