PepperCat-YamanekoVillage/NORZ/decoder/ophd/.busrq.png

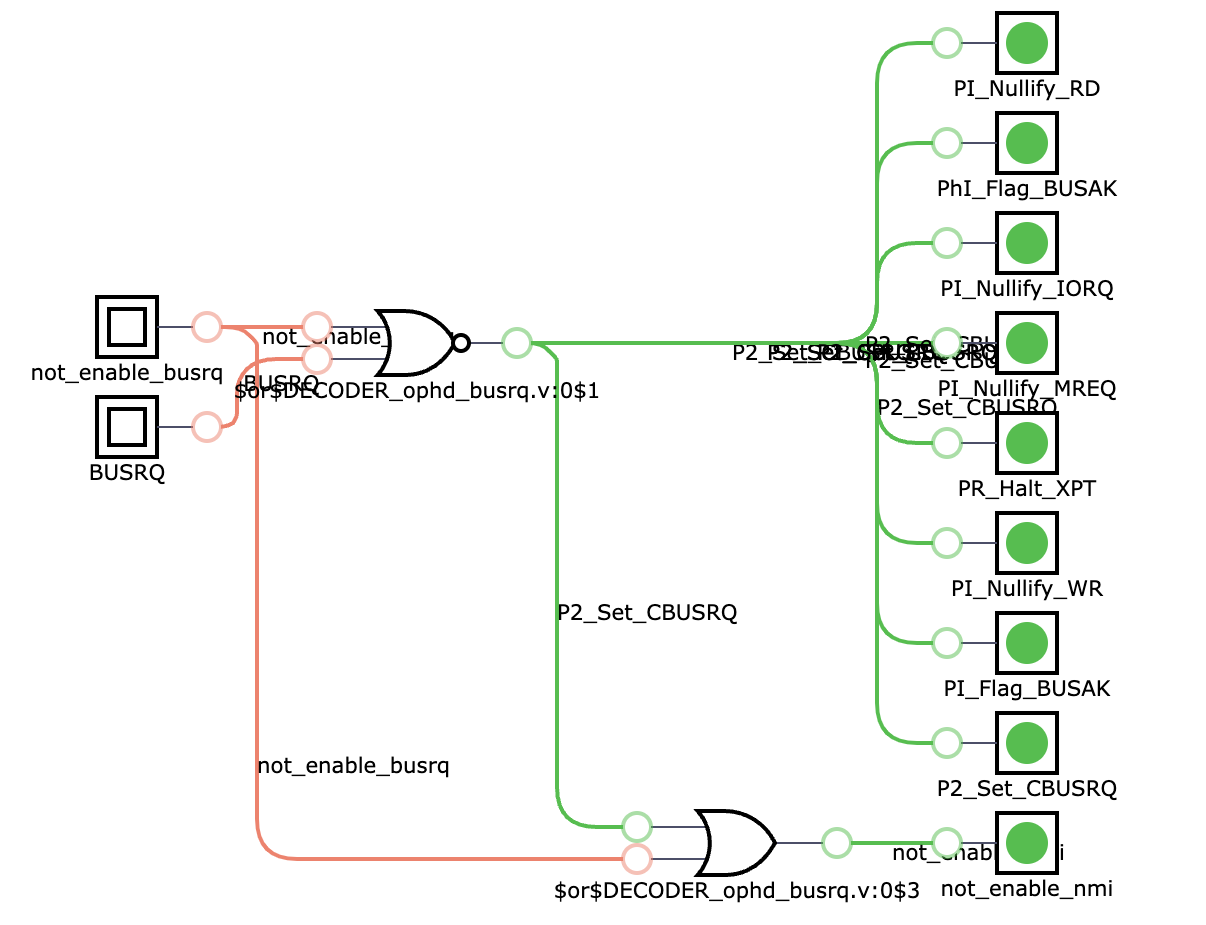
decoder/ophd/.busrq.png
