PepperCat-YamanekoVillage/NORZ/decoder/ophd/.int.png

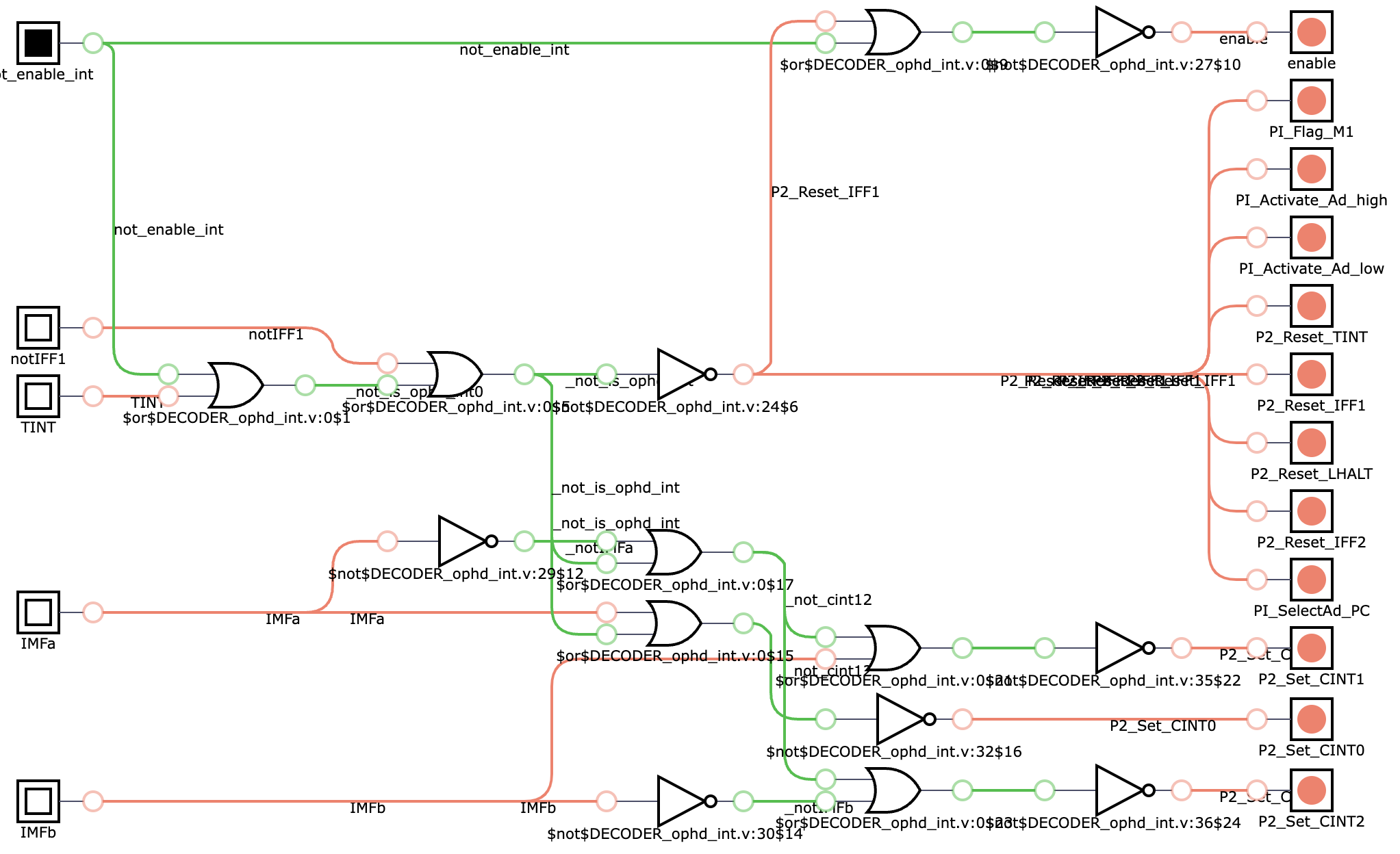
decoder/ophd/.int.png
