PepperCat-YamanekoVillage/NORZ/decoder/ophd/.nmi.png

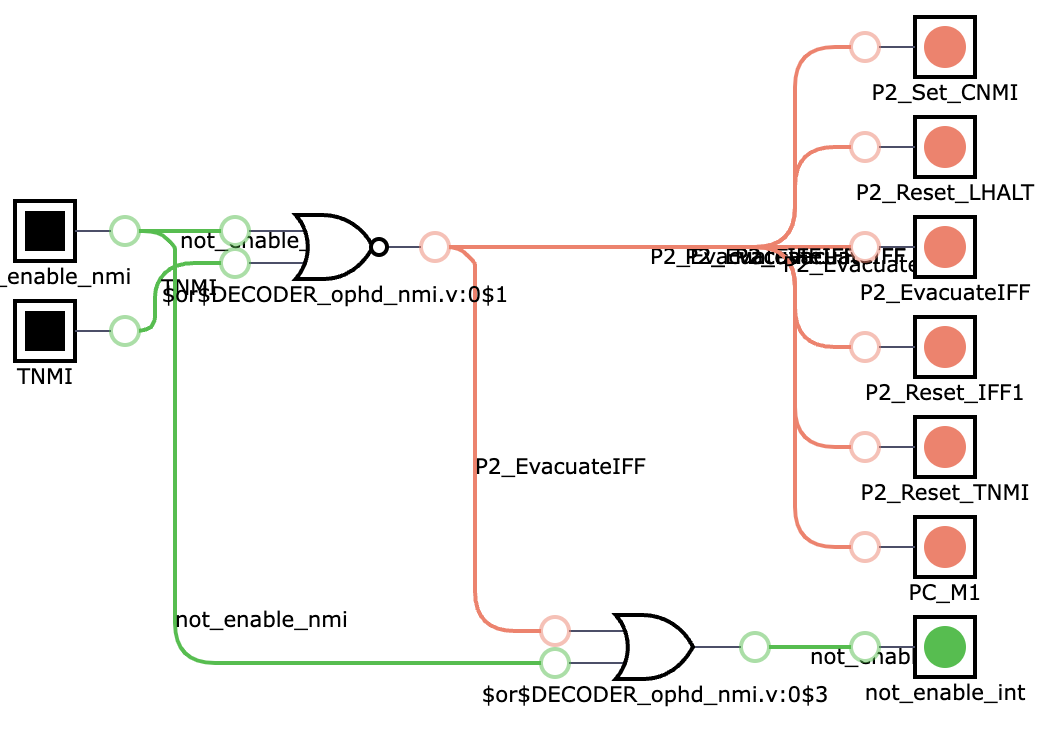
decoder/ophd/.nmi.png
