PepperCat-YamanekoVillage/NORZ/flipflop/.C.png

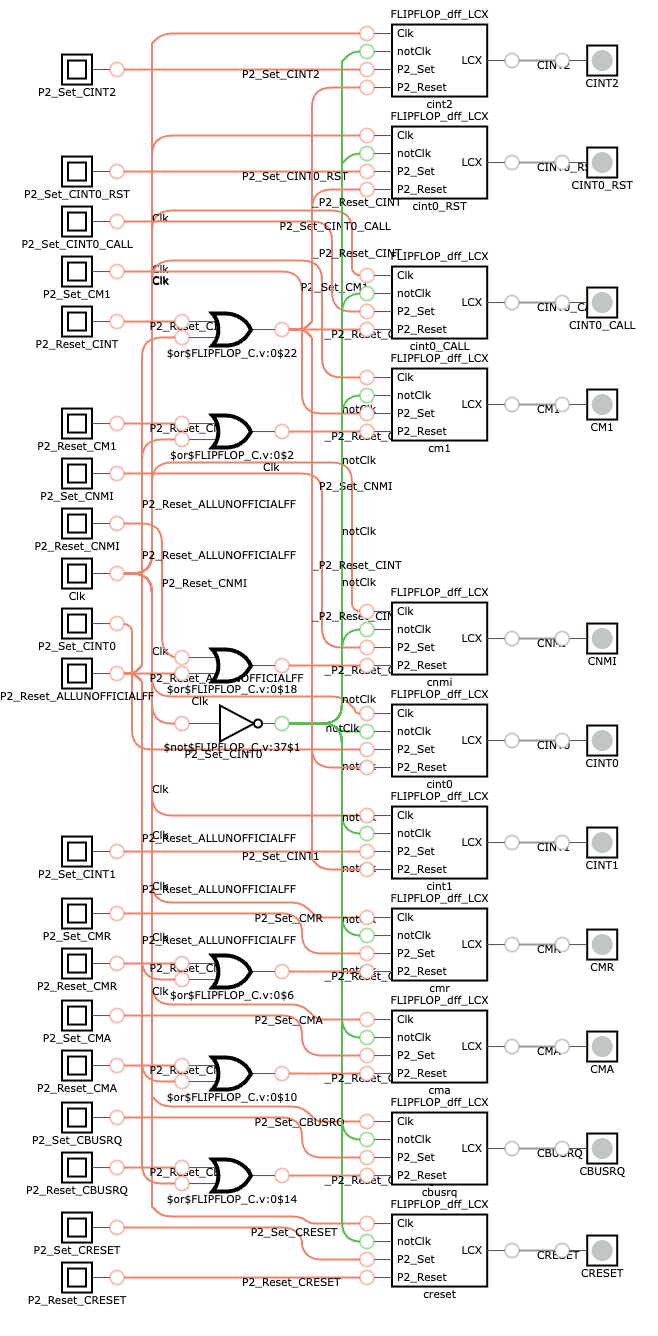
flipflop/.C.png
