PepperCat-YamanekoVillage/NORZ/flipflop/.flipflop.png

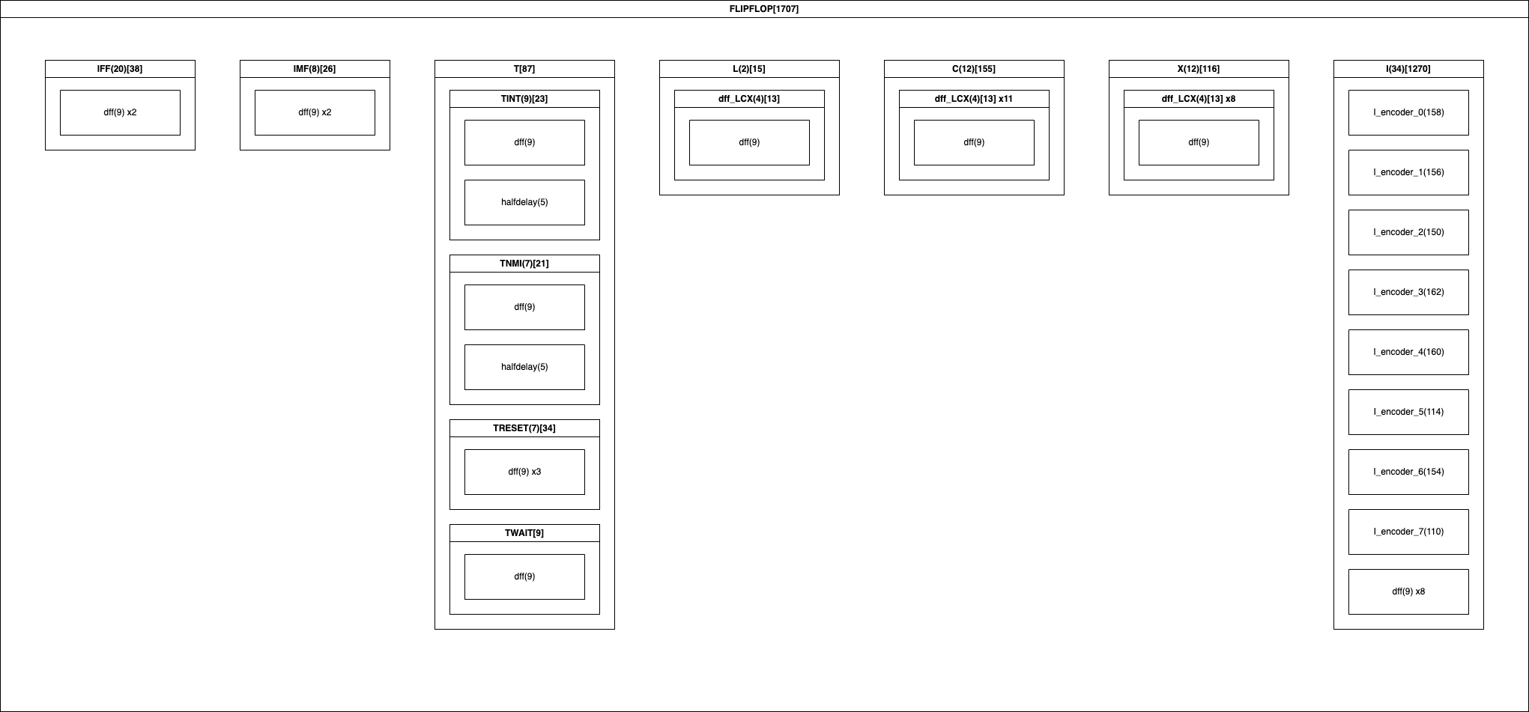
flipflop/.flipflop.png
