PepperCat-YamanekoVillage/NORZ/flipflop/.IFF.png

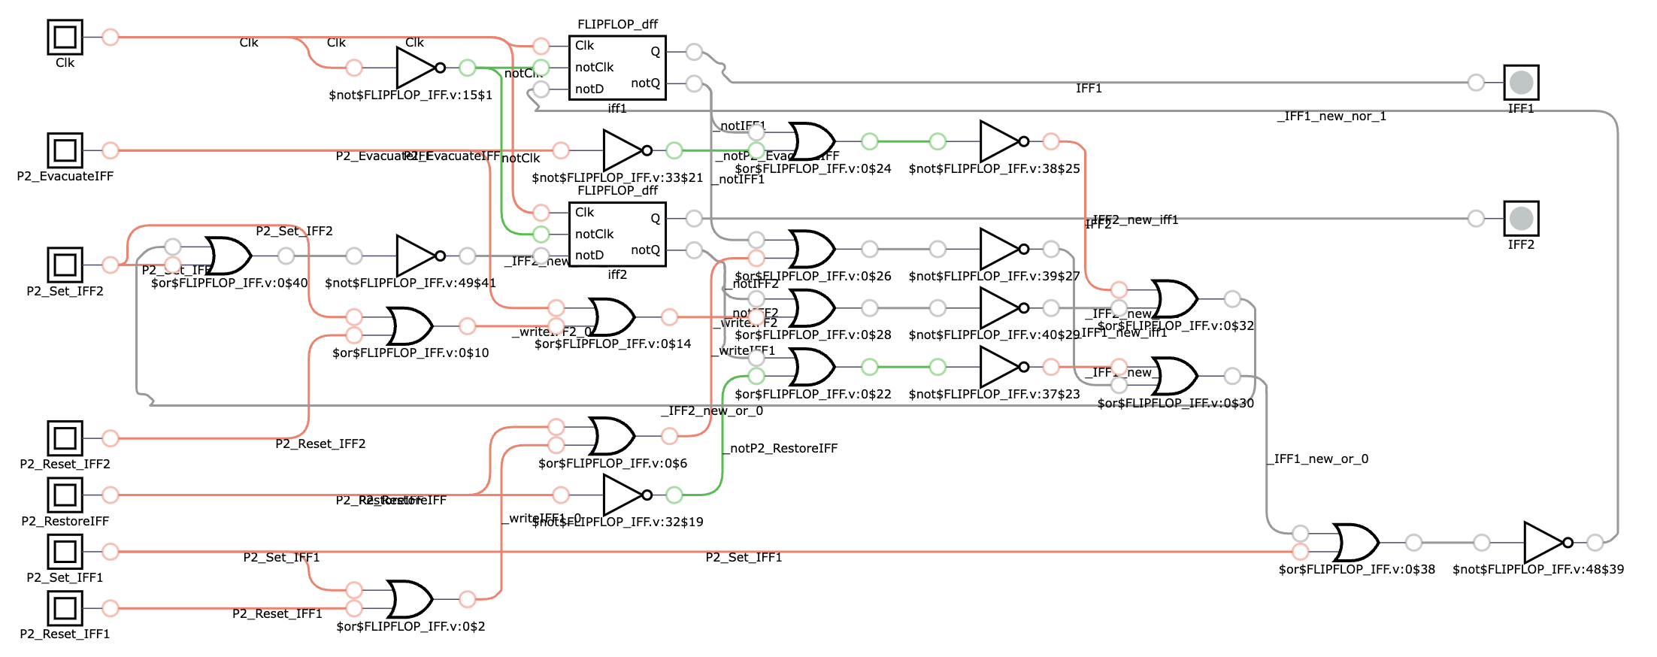
flipflop/.IFF.png
