PepperCat-YamanekoVillage/NORZ/flipflop/.IMF.png

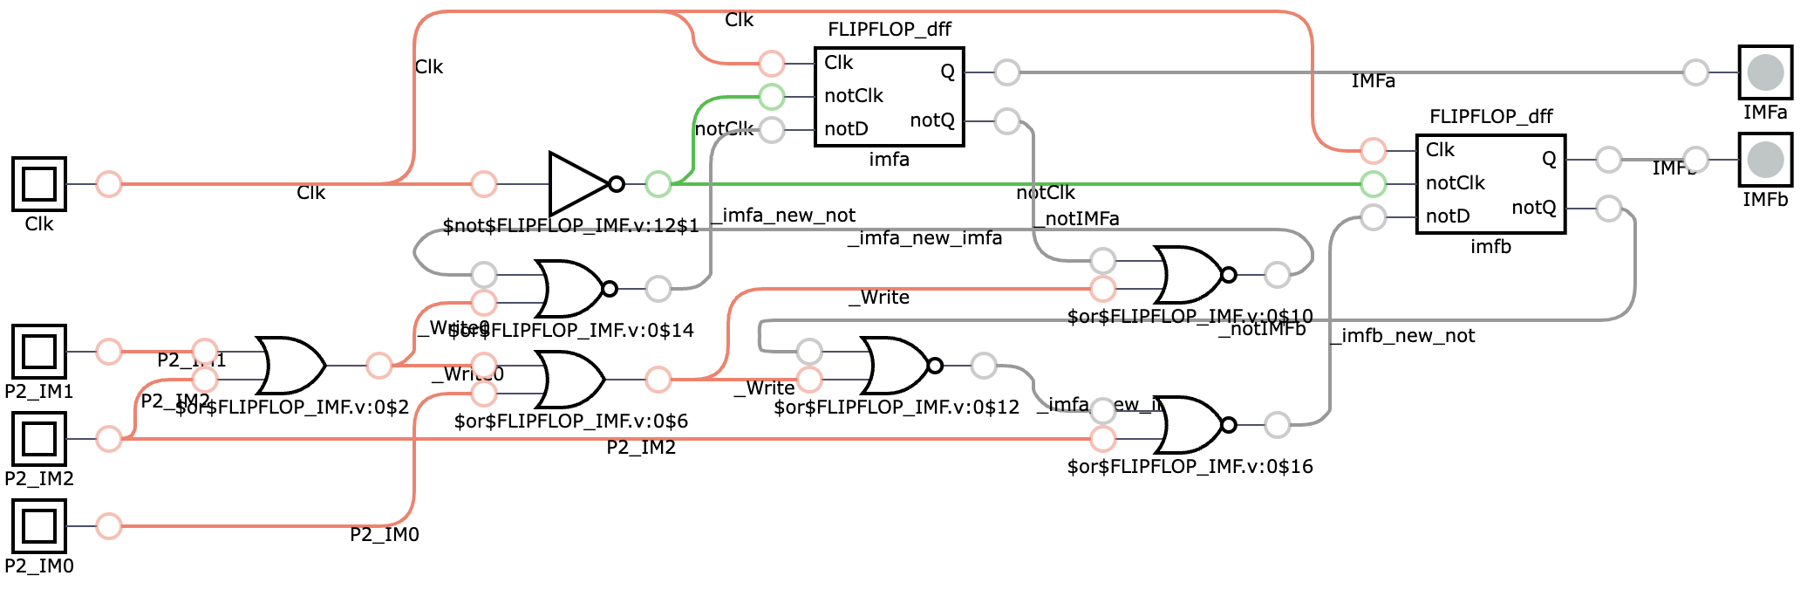
flipflop/.IMF.png
