PepperCat-YamanekoVillage/NORZ/flipflop/.L.png

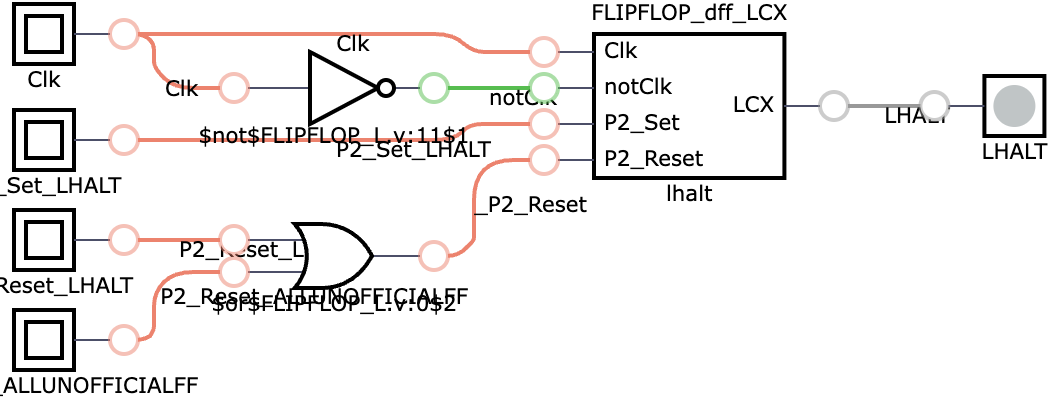
flipflop/.L.png
