PepperCat-YamanekoVillage/NORZ/flipflop/T/.TINT.png

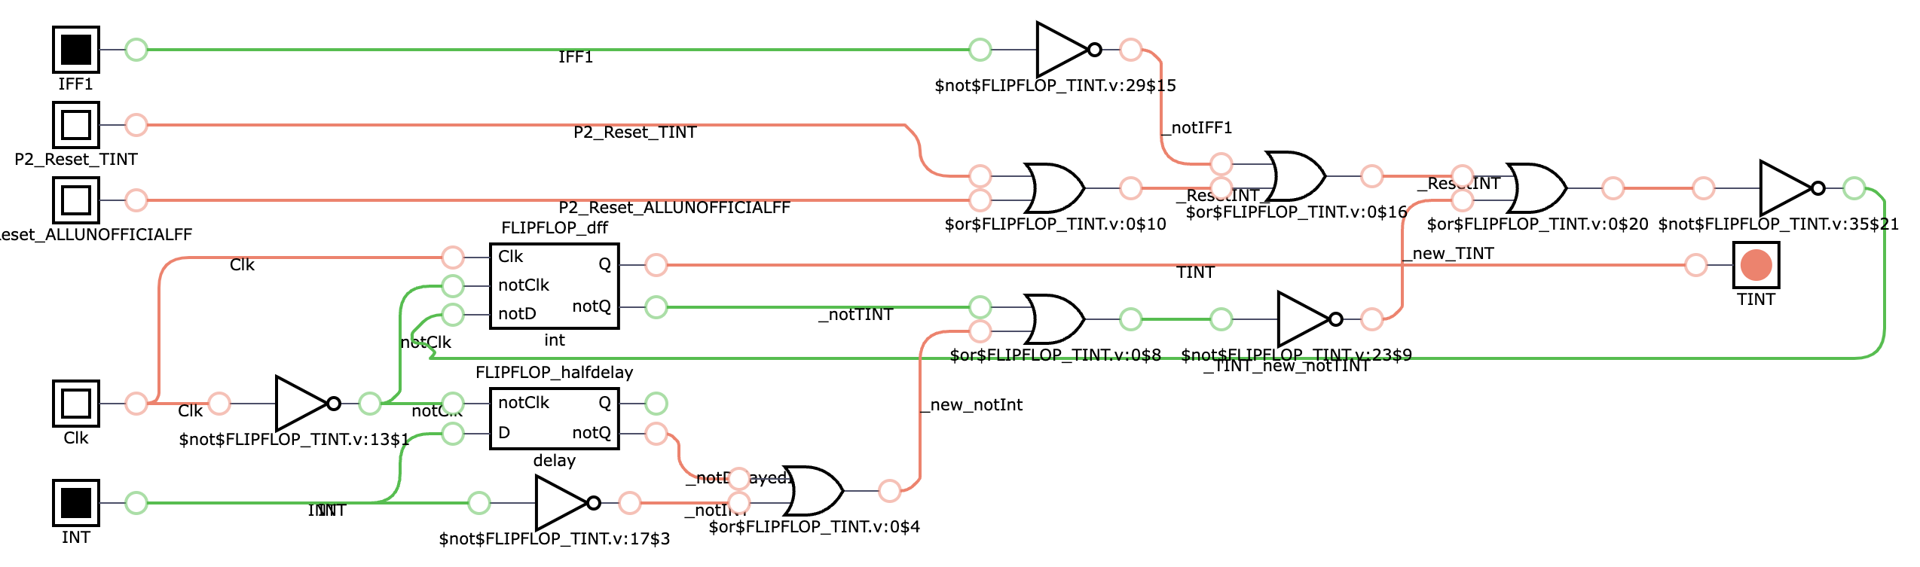
flipflop/T/.TINT.png
