PepperCat-YamanekoVillage/NORZ/flipflop/T/.TNMI.png

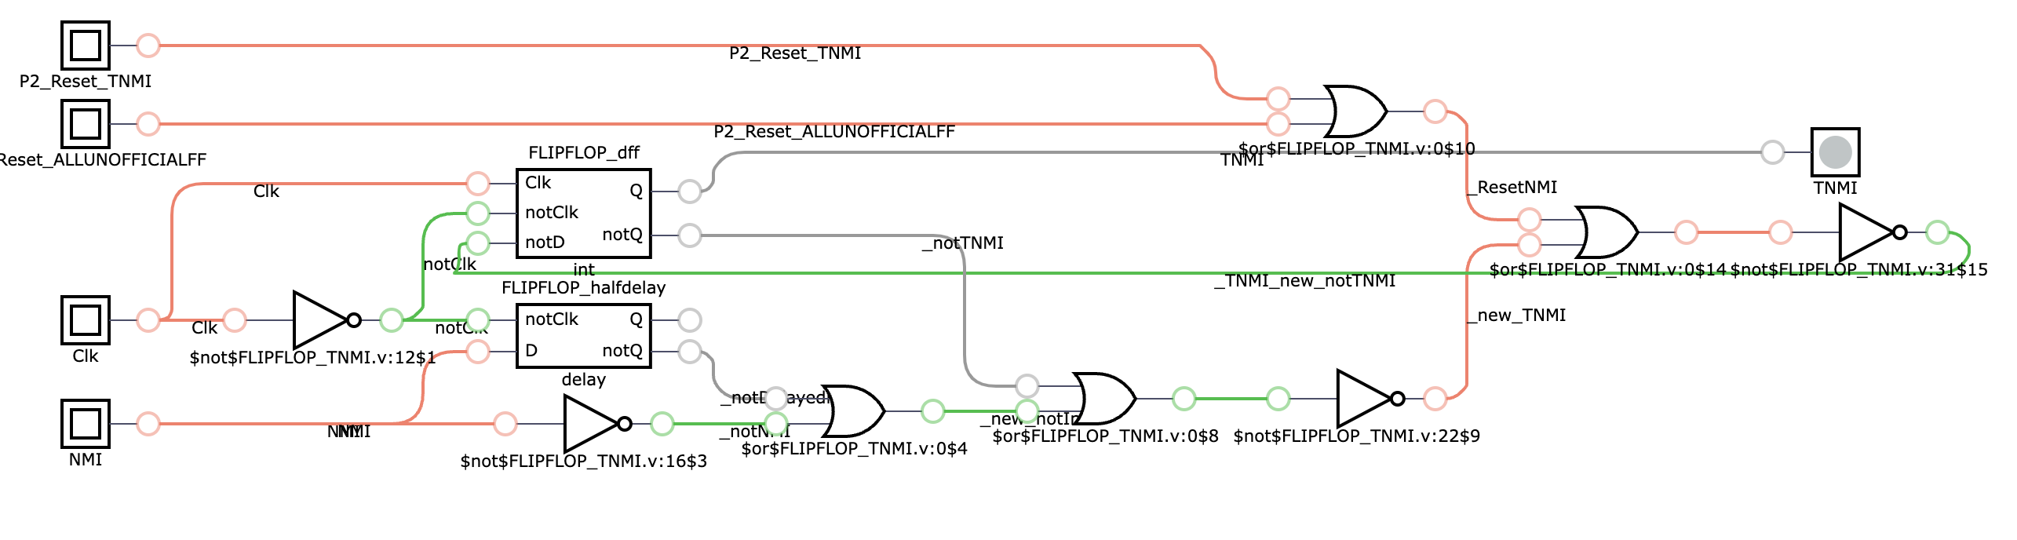
flipflop/T/.TNMI.png
