PepperCat-YamanekoVillage/NORZ/flipflop/T/.TRESET.png

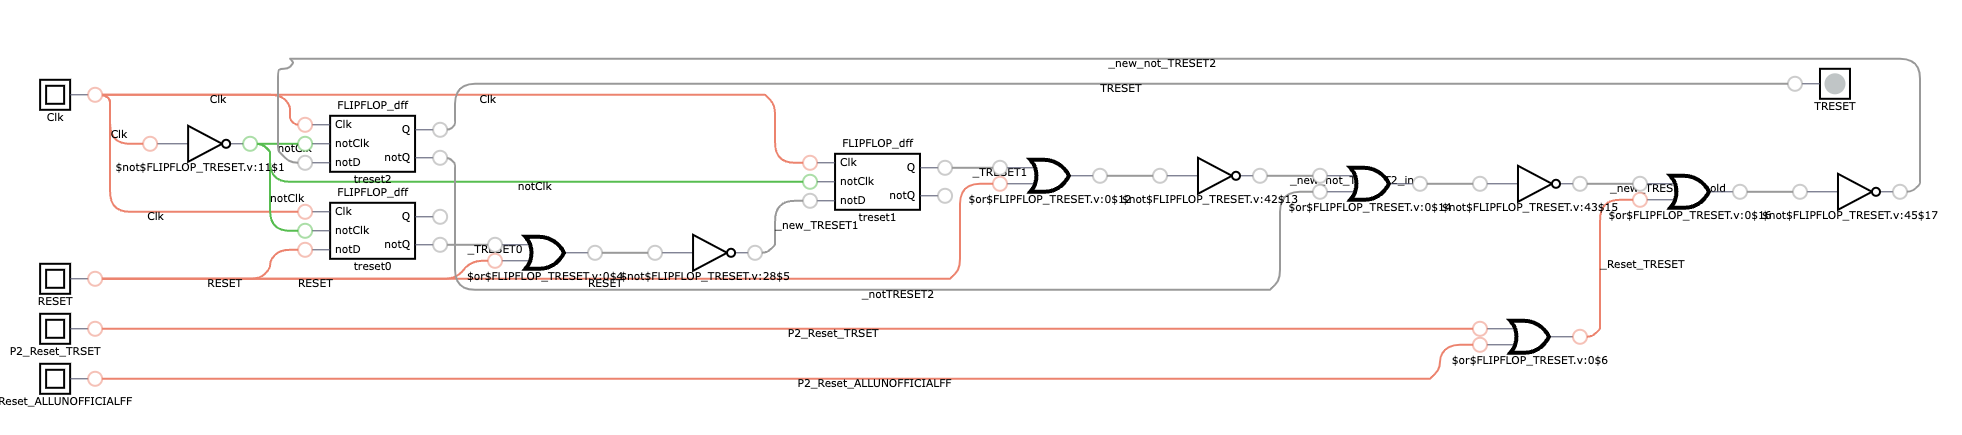
flipflop/T/.TRESET.png
