PepperCat-YamanekoVillage/NORZ/interface/.interface.png

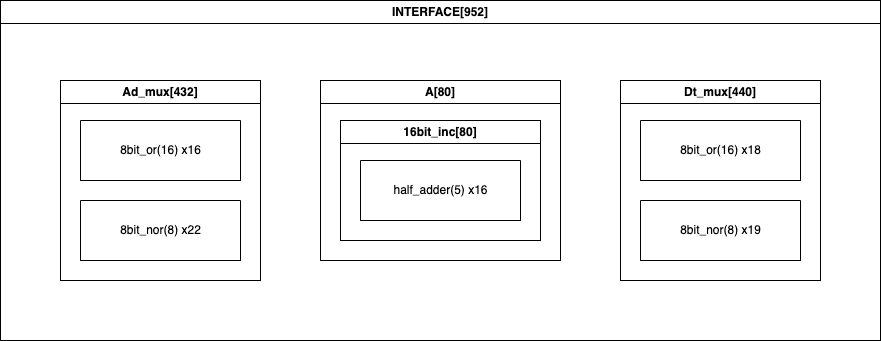
interface/.interface.png
