PepperCat-YamanekoVillage/NORZ/register/.register.png

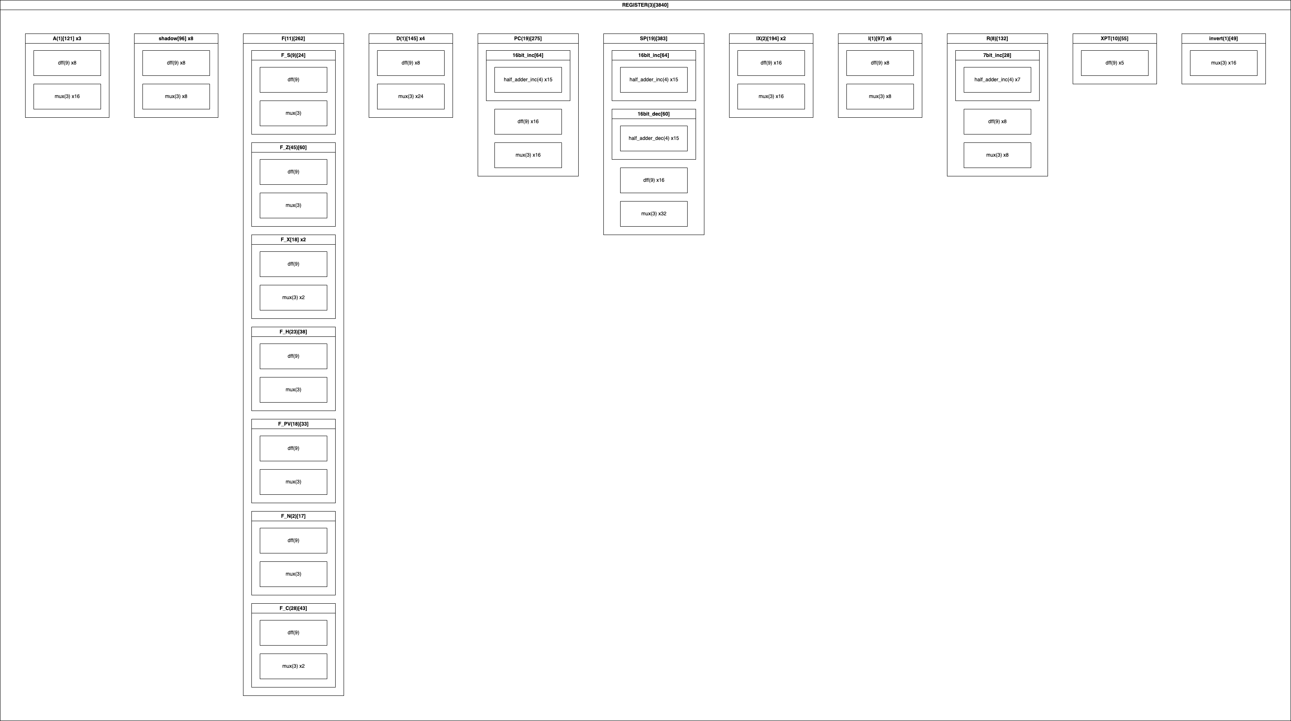
register/.register.png
