PepperCat-YamanekoVillage/NORZ/decoder/parts/.1bit_decoder.png

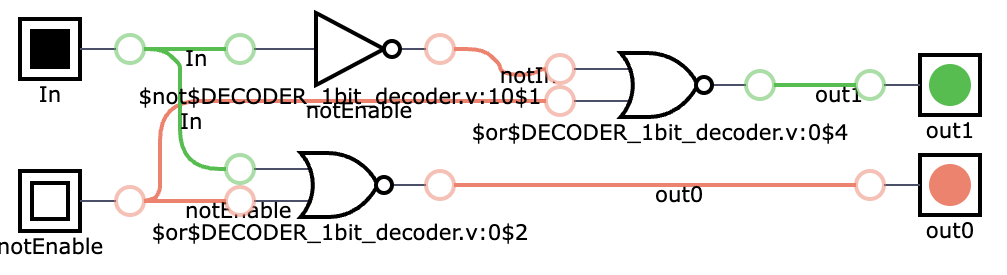
decoder/parts/.1bit_decoder.png
