PepperCat-YamanekoVillage/NORZ/register/parts/.mux.png

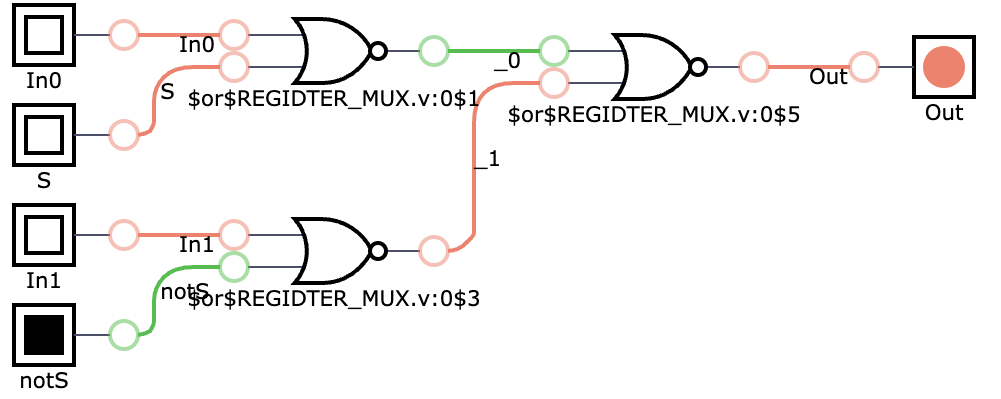
register/parts/.mux.png
