PepperCat-YamanekoVillage/NORZ/alu/.operation.png

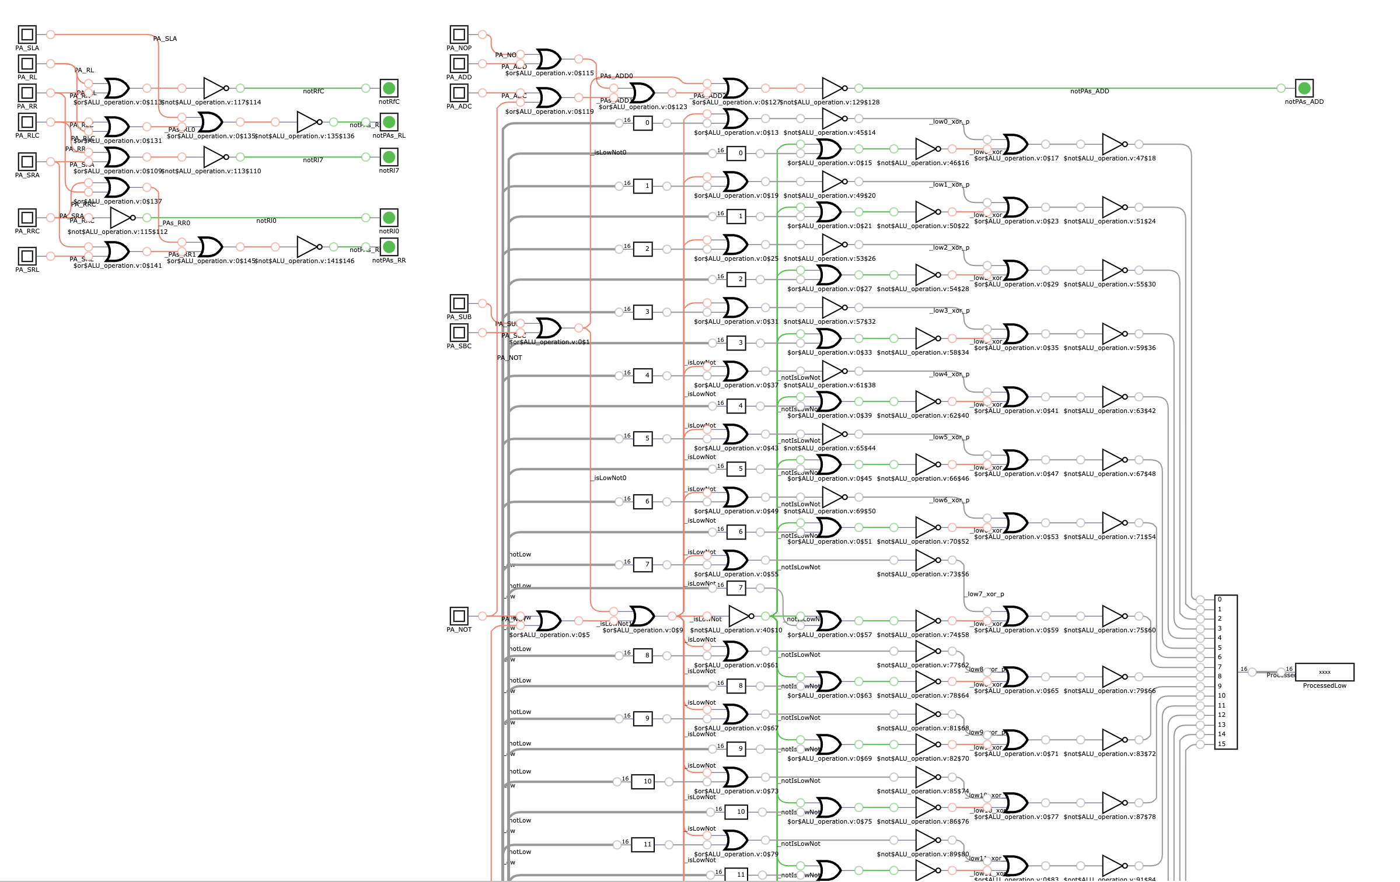
alu/.operation.png
