PepperCat-YamanekoVillage/NORZ/verilog/register/REGISTER_SP.v

// 19(383)
module REGISTER_SP(
        // input wire clk,
        input wire Clk,
        input wire notClk,
        input wire [15:0] notALUResult,
        input wire PR_Write_SP_high,
        input wire PR_Write_SP_low,
        input wire PR_Inc_SP,
        input wire PR_Dec_SP,
        output wire [15:0] SP,
        output wire [15:0] notSP
    );

    // wire Clk = clk;
    // wire notClk = ~clk;

    wire _notPR_Write_high = PR_Write_SP_high ~| PR_Write_SP_high;
    wire _notPR_Write_low = PR_Write_SP_low ~| PR_Write_SP_low;
    wire _notPR_Dec_SP = PR_Dec_SP ~| PR_Dec_SP;

    //
    // inc
    //

    wire [15:0] _Inc;

    REGISTER_16bit_inc Inc(
        .In(SP),
        .notIn(notSP),
        .CY(PR_Inc_SP),
        .Out(_Inc)
    );

    //
    // dec
    //

    wire [15:0] _notDec;

    REGISTER_16bit_dec Dec(
        .In(SP),
        .notIn(notSP),
        .notOut(_notDec)
    );

    wire _notInc0 = _Inc[0] ~| _Inc[0];
    wire _notInc1 = _Inc[1] ~| _Inc[1];
    wire _notInc2 = _Inc[2] ~| _Inc[2];
    wire _notInc3 = _Inc[3] ~| _Inc[3];
    wire _notInc4 = _Inc[4] ~| _Inc[4];
    wire _notInc5 = _Inc[5] ~| _Inc[5];
    wire _notInc6 = _Inc[6] ~| _Inc[6];
    wire _notInc7 = _Inc[7] ~| _Inc[7];
    wire _notInc8 = _Inc[8] ~| _Inc[8];
    wire _notInc9 = _Inc[9] ~| _Inc[9];
    wire _notInc10 = _Inc[10] ~| _Inc[10];
    wire _notInc11 = _Inc[11] ~| _Inc[11];
    wire _notInc12 = _Inc[12] ~| _Inc[12];
    wire _notInc13 = _Inc[13] ~| _Inc[13];
    wire _notInc14 = _Inc[14] ~| _Inc[14];
    wire _notInc15 = _Inc[15] ~| _Inc[15];

    wire _not_m0;
    wire _not_m1;
    wire _not_m2;
    wire _not_m3;
    wire _not_m4;
    wire _not_m5;
    wire _not_m6;
    wire _not_m7;
    wire _not_m8;
    wire _not_m9;
    wire _not_m10;
    wire _not_m11;
    wire _not_m12;
    wire _not_m13;
    wire _not_m14;
    wire _not_m15;
    wire _not_newSP0;
    wire _not_newSP1;
    wire _not_newSP2;
    wire _not_newSP3;
    wire _not_newSP4;
    wire _not_newSP5;
    wire _not_newSP6;
    wire _not_newSP7;
    wire _not_newSP8;
    wire _not_newSP9;
    wire _not_newSP10;
    wire _not_newSP11;
    wire _not_newSP12;
    wire _not_newSP13;
    wire _not_newSP14;
    wire _not_newSP15;

    REGISTER_mux m0_1(
        .S(PR_Dec_SP),
        .notS(_notPR_Dec_SP),
        .N(_notInc0),
        .P(_notDec[0]),
        .Out(_not_m0)
    );

    REGISTER_mux m0_2(
        .S(PR_Write_SP_low),
        .notS(_notPR_Write_low),
        .N(_not_m0),
        .P(notALUResult[0]),
        .Out(_not_newSP0)
    );

    REGISTER_mux m1_1(
        .S(PR_Dec_SP),
        .notS(_notPR_Dec_SP),
        .N(_notInc1),
        .P(_notDec[1]),
        .Out(_not_m1)
    );

    REGISTER_mux m1_2(
        .S(PR_Write_SP_low),
        .notS(_notPR_Write_low),
        .N(_not_m1),
        .P(notALUResult[1]),
        .Out(_not_newSP1)
    );

    REGISTER_mux m2_1(
        .S(PR_Dec_SP),
        .notS(_notPR_Dec_SP),
        .N(_notInc2),
        .P(_notDec[2]),
        .Out(_not_m2)
    );

    REGISTER_mux m2_2(
        .S(PR_Write_SP_low),
        .notS(_notPR_Write_low),
        .N(_not_m2),
        .P(notALUResult[2]),
        .Out(_not_newSP2)
    );

    REGISTER_mux m3_1(
        .S(PR_Dec_SP),
        .notS(_notPR_Dec_SP),
        .N(_notInc3),
        .P(_notDec[3]),
        .Out(_not_m3)
    );

    REGISTER_mux m3_2(
        .S(PR_Write_SP_low),
        .notS(_notPR_Write_low),
        .N(_not_m3),
        .P(notALUResult[3]),
        .Out(_not_newSP3)
    );

    REGISTER_mux m4_1(
        .S(PR_Dec_SP),
        .notS(_notPR_Dec_SP),
        .N(_notInc4),
        .P(_notDec[4]),
        .Out(_not_m4)
    );

    REGISTER_mux m4_2(
        .S(PR_Write_SP_low),
        .notS(_notPR_Write_low),
        .N(_not_m4),
        .P(notALUResult[4]),
        .Out(_not_newSP4)
    );

    REGISTER_mux m5_1(
        .S(PR_Dec_SP),
        .notS(_notPR_Dec_SP),
        .N(_notInc5),
        .P(_notDec[5]),
        .Out(_not_m5)
    );

    REGISTER_mux m5_2(
        .S(PR_Write_SP_low),
        .notS(_notPR_Write_low),
        .N(_not_m5),
        .P(notALUResult[5]),
        .Out(_not_newSP5)
    );

    REGISTER_mux m6_1(
        .S(PR_Dec_SP),
        .notS(_notPR_Dec_SP),
        .N(_notInc6),
        .P(_notDec[6]),
        .Out(_not_m6)
    );

    REGISTER_mux m6_2(
        .S(PR_Write_SP_low),
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
        .Clk(Clk),
        .notClk(notClk),
        .notD(_not_newSP14),
        .Q(SP[14]),
        .notQ(notSP[14])
    );

    REGISTER_dff SP15(
        .Clk(Clk),
        .notClk(notClk),
        .notD(_not_newSP15),
        .Q(SP[15]),
        .notQ(notSP[15])
    );

endmodule
