PepperCat-YamanekoVillage/NORZ/verilog/register/REGISTER_PC.v

// 18(275)
module REGISTER_PC(
        // input wire clk,
        input wire Clk,
        input wire notClk,
        input wire [15:0] notALUResult,
        input wire PR_Write_PC_high,
        input wire PR_Write_PC_low,
        input wire PR_Inc_PC,
        output wire [15:0] PC,
        output wire [15:0] notPC
    );

    // wire Clk = clk;
    // wire notClk = ~Clk;

    wire _notPR_Write_high = PR_Write_PC_high ~| PR_Write_PC_high;
    wire _notPR_Write_low = PR_Write_PC_low ~| PR_Write_PC_low;

    //
    // inc
    //

    wire [15:0] _Inc;

    REGISTER_16bit_inc Inc(
        .In(PC),
        .notIn(notPC),
        .CY(PR_Inc_PC),
        .Out(_Inc)
    );

    wire _new_notPC0;
    wire _new_notPC1;
    wire _new_notPC2;
    wire _new_notPC3;
    wire _new_notPC4;
    wire _new_notPC5;
    wire _new_notPC6;
    wire _new_notPC7;
    wire _new_notPC8;
    wire _new_notPC9;
    wire _new_notPC10;
    wire _new_notPC11;
    wire _new_notPC12;
    wire _new_notPC13;
    wire _new_notPC14;
    wire _new_notPC15;

    wire _notInc0 = _Inc[0] ~| _Inc[0];
    wire _notInc1 = _Inc[1] ~| _Inc[1];
    wire _notInc2 = _Inc[2] ~| _Inc[2];
    wire _notInc3 = _Inc[3] ~| _Inc[3];
    wire _notInc4 = _Inc[4] ~| _Inc[4];
    wire _notInc5 = _Inc[5] ~| _Inc[5];
    wire _notInc6 = _Inc[6] ~| _Inc[6];
    wire _notInc7 = _Inc[7] ~| _Inc[7];
    wire _notInc8 = _Inc[8] ~| _Inc[8];
    wire _notInc9 = _Inc[9] ~| _Inc[9];
    wire _notInc10 = _Inc[10] ~| _Inc[10];
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
        .Clk(Clk),
        .notClk(notClk),
        .notD(_new_notPC14),
        .Q(PC[14]),
        .notQ(notPC[14])
    );

    REGISTER_dff PC15(
        .Clk(Clk),
        .notClk(notClk),
        .notD(_new_notPC15),
        .Q(PC[15]),
        .notQ(notPC[15])
    );

endmodule
